dave18/SpecNext_MiSTER_Board/Source/rtl/zxnext.vhd

-- ZX Spectrum Next Implementation
-- Copyright 2020 Alvin Albrecht, Victor Trucco and Fabio Belavenuto
--
-- TBBlue - Victor Trucco & Fabio Belavenuto
-- ZXNext Refactor - Alvin Albrecht
--
-- This file is part of the ZX Spectrum Next Project
-- <https://gitlab.com/SpectrumNext/ZX_Spectrum_Next_FPGA/tree/master/cores>
--
-- The ZX Spectrum Next FPGA source code is free software: you can 
-- redistribute it and/or modify it under the terms of the GNU General 
-- Public License as published by the Free Software Foundation, either 
-- version 3 of the License, or (at your option) any later version.
--
-- The ZX Spectrum Next FPGA source code is distributed in the hope 
-- that it will be useful, but WITHOUT ANY WARRANTY; without even the 
-- implied warranty of MERCHANTABILITY or FITNESS FOR A PARTICULAR 
-- PURPOSE.  See the GNU General Public License for more details.
--
-- You should have received a copy of the GNU General Public License
-- along with the ZX Spectrum Next FPGA source code.  If not, see 
-- <https://www.gnu.org/licenses/>.

library ieee;
use ieee.std_logic_1164.all;
use IEEE.NUMERIC_STD.ALL;
use IEEE.std_logic_unsigned.ALL;
use work.Z80N_pack.all;

entity zxnext is
   generic
   (
      g_machine_id         : unsigned(7 downto 0);
      g_version            : unsigned(7 downto 0);
      g_sub_version        : unsigned(7 downto 0)
   );
   port (
      -- CLOCK
      
      i_CLK_28             : in std_logic;      -- 28MHz for machine logic
      i_CLK_28_n           : in std_logic;      -- 28MHz inverted
      i_CLK_14             : in std_logic;      -- 14MHz hi-res pixel clock
      i_CLK_7              : in std_logic;      -- 7MHz pixel clock
      i_CLK_CPU            : in std_logic;      -- CPU clock adjusted for speed and contention
      i_CLK_PSG_EN         : in std_logic;      -- 28MHz clock enable for PSG

      o_CPU_SPEED          : out std_logic_vector(1 downto 0);    -- cpu speed selection 00 = 3.5, 01 = 7, 10 = 14, 11 = 28
      o_CPU_CONTEND        : out std_logic;     -- indicates cpu is contended
      o_CPU_CLK_LSB        : out std_logic;     -- the contended cpu clock is derived from the pixel counter lsb
      
      -- RESET

      i_RESET_HARD         : in std_logic;      -- reboot in config mode, duration counted in top module
      i_RESET_SOFT         : in std_logic;      -- reset current system, duration counted in top module
      
      o_RESET_SOFT         : out std_logic;     -- asserted for one cycle at 28MHz
      o_RESET_HARD         : out std_logic;     -- asserted for one cycle at 28MHz
      o_RESET_PERIPHERAL   : out std_logic;     -- asserted under sw control for esp / exp bus reset
      
      -- FLASH BOOT
      
      o_FLASH_BOOT         : out std_logic;                       -- load new core
      o_CORE_ID            : out std_logic_vector(4 downto 0);    -- core id 0-31
      
      -- SPECIAL KEYS

      i_SPKEY_FUNCTION     : in std_logic_vector(10 downto 1);    -- F10 through F1
      i_SPKEY_BUTTONS      : in std_logic_vector(1 downto 0);     -- raw state of nmi buttons m1(0) & drive(1)
      
      -- MEMBRANE KEYBOARD
      
      o_KBD_CANCEL         : out std_logic;                       -- cancel entering extended keys into standard 8x5 matrix
      
      o_KBD_ROW            : out std_logic_vector(7 downto 0);    -- A15:A8 in keyboard read
      i_KBD_COL            : in std_logic_vector(4 downto 0);     -- D4:D0 in keyboard read (D6:D5 are the new keys)
      
      i_KBD_EXTENDED_KEYS  : in std_logic_vector(15 downto 0);    -- state of extended keys independent of matrix
      
      -- PS/2 KEYBOARD SETUP
      
      o_KEYMAP_ADDR        : out std_logic_vector(8 downto 0);    -- keymap address
      o_KEYMAP_DATA        : out std_logic_vector(7 downto 0);    -- keymap data
      o_KEYMAP_WE          : out std_logic;                       -- write signal
      
      -- JOYSTICK
      
      i_JOY_LEFT           : in std_logic_vector(10 downto 0);    -- active high  X Z Y START A C B U D L R
      i_JOY_RIGHT          : in std_logic_vector(10 downto 0);    -- active high  X Z Y START A C B U D L R
      
      o_JOY_IO_MODE_EN     : out std_logic;                       -- joystick io mode enabled
      o_JOY_IO_MODE_PIN_7  : out std_logic;                       -- state of pin 7 if in joystick io mode
		
		o_JOY_LEFT_TYPE      : out std_logic_vector(2 downto 0);        -- left joystick type --additional code 
		o_JOY_RIGHT_TYPE     : out std_logic_vector(2 downto 0);        -- right joystick type --additional code
      
      -- MOUSE
      
      i_MOUSE_X            : in std_logic_vector(7 downto 0);
      i_MOUSE_Y            : in std_logic_vector(7 downto 0);
      i_MOUSE_BUTTON       : in std_logic_vector(2 downto 0);     -- M, R, L
      i_MOUSE_WHEEL        : in std_logic_vector(3 downto 0);
      
      o_PS2_MODE           : out std_logic;
      o_MOUSE_CONTROL      : out std_logic_vector(2 downto 0);    -- Button reverse, DPI(1:0)
      
      -- I2C
      
      i_I2C_SCL_n          : in std_logic;
      i_I2C_SDA_n          : in std_logic;
      
      o_I2C_SCL_n          : out std_logic;     -- 0 = assert, 1 = tristate
      o_I2C_SDA_n          : out std_logic;     -- 0 = assert, 1 = tristate
      
      -- SPI

      o_SPI_SS_FLASH_n     : out std_logic;
      o_SPI_SS_SD1_n       : out std_logic;
      o_SPI_SS_SD0_n       : out std_logic;

      o_SPI_SCK            : out std_logic;
      o_SPI_MOSI           : out std_logic;
      
      i_SPI_SD_MISO        : in std_logic;
      i_SPI_FLASH_MISO     : in std_logic;
      
      -- UART
      
      i_UART0_RX           : in std_logic;
      o_UART0_TX           : out std_logic;
      
      -- VIDEO
      -- synchronized to i_CLK_14
      
      o_RGB                : out std_logic_vector(8 downto 0);    -- RGB333
      o_RGB_CS_n           : out std_logic;                       -- csync
      o_RGB_VS_n           : out std_logic;                       -- vsync
      o_RGB_HS_n           : out std_logic;                       -- hsync
      o_RGB_VB_n           : out std_logic;                       -- vblank
      o_RGB_HB_n           : out std_logic;                       -- hblank
      
      o_VIDEO_50_60        : out std_logic;                       -- 0 = 50Hz, 1 = 60Hz
      o_VIDEO_SCANLINES    : out std_logic_vector(1 downto 0);    -- 
      o_VIDEO_SCANDOUBLE   : out std_logic;                       -- 
      
      o_VIDEO_MODE         : out std_logic_vector(2 downto 0);    -- video mode: VGA 0-6, HDMI
      o_MACHINE_TIMING     : out std_logic_vector(2 downto 0);    -- machine timing: 00X = 48k, 010 = 128k, 011 = +3, 100 = pentagon
      
      o_HDMI_RESET         : out std_logic;
      
      -- AUDIO
      
      o_AUDIO_HDMI_AUDIO_EN : out std_logic;

      o_AUDIO_SPEAKER_EN   : out std_logic;     -- enable internal speaker
      o_AUDIO_SPEAKER_BEEP : out std_logic;     -- only beep to internal speaker
      
      i_AUDIO_EAR          : in std_logic;      -- tape in
      o_AUDIO_MIC          : out std_logic;     -- tape out
      
      o_AUDIO_SPEAKER_EAR  : out std_logic;
      o_AUDIO_SPEAKER_MIC  : out std_logic;

      o_AUDIO_L            : out std_logic_vector(12 downto 0);   -- pcm audio
      o_AUDIO_R            : out std_logic_vector(12 downto 0);   -- pcm audio

      -- EXTERNAL SRAM (synchronized to i_CLK_28)
      -- memory transactions complete after one cycle, data read is registered a cycle later but is available asap
      
      -- Port A is read/write and highest priority (CPU)
      
      o_RAM_A_ADDR         : out std_logic_vector(20 downto 0);   -- 2MB memory space
      o_RAM_A_REQ          : out std_logic;                       -- '1' indicates memory request on next rising edge
      o_RAM_A_RD           : out std_logic;                       -- '1' for read, '0' for write
      i_RAM_A_DI           : in std_logic_vector(7 downto 0);     -- data read from memory
      o_RAM_A_DO           : out std_logic_vector(7 downto 0);    -- data written to memory
		
		i_CPU_WAIT           : in std_logic := '0';
      
      -- Port B is read only (LAYER 2)
      
      o_RAM_B_ADDR         : out std_logic_vector(20 downto 0);   -- 2MB memory space
      o_RAM_B_REQ_T        : out std_logic;                       -- toggle indicates memory request
      i_RAM_B_DI           : in std_logic_vector(7 downto 0);     -- data read from memory
      
      -- EXPANSION BUS
      
      o_BUS_ADDR           : out std_logic_vector(15 downto 0);   -- unidirectional address bus = no external DMA for now
      i_BUS_DI             : in std_logic_vector(7 downto 0);     -- data bus in from external connector
      o_BUS_DO             : out std_logic_vector(7 downto 0);    -- data bus out to external connector
      o_BUS_MREQ_n         : out std_logic;
      o_BUS_IORQ_n         : out std_logic;
      o_BUS_RD_n           : out std_logic;
      o_BUS_WR_n           : out std_logic;
      o_BUS_M1_n           : out std_logic;
      i_BUS_WAIT_n         : in std_logic;
      i_BUS_NMI_n          : in std_logic;
      i_BUS_INT_n          : in std_logic;
      o_BUS_INT_n          : out std_logic;
      i_BUS_BUSREQ_n       : in std_logic;
      o_BUS_BUSAK_n        : out std_logic;
      o_BUS_HALT_n         : out std_logic;
      o_BUS_RFSH_n         : out std_logic;
--    o_BUS_IEO            : out std_logic;
      
      i_BUS_ROMCS_n        : in std_logic;                        -- 1 disables internal rom
--    i_BUS_RAMCS_n        : in std_logic;
      i_BUS_IORQULA_n      : in std_logic;                        -- 1 disables port fe
      
      o_BUS_EN             : out std_logic;                       -- enable the expansion bus, changes on rising edge of cpu clock
      o_BUS_CLKEN          : out std_logic;                       -- 1 to keep 3.5MHz clock on the expansion bus even when off
      
      o_BUS_NMI_DEBOUNCE_DISABLE  : out std_logic;
      
      -- ESP GPIO
      
      i_ESP_GPIO_20        : in std_logic_vector(2 downto 0);
      
      o_ESP_GPIO_0         : out std_logic;
      o_ESP_GPIO_0_EN      : out std_logic;                       -- 0 = high Z
      
      -- PI GPIO
      
      i_GPIO               : in std_logic_vector(27 downto 0);
      
      o_GPIO               : out std_logic_vector(27 downto 0);
      o_GPIO_EN            : out std_logic_vector(27 downto 0)    -- 0 = high Z
   );
end entity;

architecture rtl of zxnext is

   -- RESET
   
   signal reset                  : std_logic;
   signal reset_soft             : std_logic;
   signal reset_hard             : std_logic;
   
   -- Z80 & DMA
   
   signal z80_wait_n             : std_logic;
   signal z80_int_n              : std_logic;
   signal z80_nmi_n              : std_logic;
   signal z80_busrq_n            : std_logic;
   signal z80_m1_n               : std_logic;
   signal z80_mreq_n             : std_logic;
   signal z80_iorq_n             : std_logic;
   signal z80_rd_n               : std_logic;
   signal z80_wr_n               : std_logic;
   signal z80_rfsh_n             : std_logic;
   signal z80_halt_n             : std_logic;
   signal z80_busak_n            : std_logic;
   signal z80_a                  : std_logic_vector(15 downto 0);
   signal z80_do                 : std_logic_vector(7 downto 0);
   signal Z80N_dout_s            : std_logic;
   signal Z80N_data_s            : std_logic_vector(15 downto 0);
   signal Z80N_command_s         : Z80N_seq;

   signal dma_wait_n             : std_logic;
   signal dma_busrq_n            : std_logic;
   signal dma_a                  : std_logic_vector(15 downto 0);
   signal dma_do                 : std_logic_vector(7 downto 0);
   signal dma_rd_n               : std_logic;
   signal dma_wr_n               : std_logic;
   signal dma_mreq_n             : std_logic;
   signal dma_iorq_n             : std_logic;
   
   signal port_dma_dat_0         : std_logic_vector(7 downto 0);
   signal port_dma_dat           : std_logic_vector(7 downto 0);
   signal dma_mode               : std_logic := '0';
   
   signal dma_holds_bus          : std_logic;
   signal cpu_m1_n               : std_logic;
   signal cpu_mreq_n             : std_logic;
   signal cpu_iorq_n             : std_logic;
   signal cpu_rd_n               : std_logic;
   signal cpu_wr_n               : std_logic;
   signal cpu_rfsh_n             : std_logic;
   signal cpu_halt_n             : std_logic;
   signal cpu_a                  : std_logic_vector(15 downto 0);
   signal cpu_di                 : std_logic_vector(7 downto 0);
   signal cpu_do                 : std_logic_vector(7 downto 0);
   
   signal im2_ieo                : std_logic;
   signal im2_reti_decode        : std_logic;
   signal z80_reti_seen_t3       : std_logic;
   signal z80_retn_seen_t3       : std_logic;
   signal z80_retn_seen_28       : std_logic;
   signal z80_retn_seen_28_d     : std_logic;
   signal dma_delay              : std_logic;
   signal im2_dma_delay          : std_logic;
   
   signal im2_int_req            : std_logic_vector(13 downto 0);
   signal im2_int_en             : std_logic_vector(13 downto 0);
   signal im2_status_clear       : std_logic_vector(13 downto 0);
   signal im2_dma_int_en         : std_logic_vector(13 downto 0);
   signal im2_int_status         : std_logic_vector(13 downto 0);
   signal im2_int_n              : std_logic;
   signal pulse_int_en           : std_logic;
   signal im2_dma_int            : std_logic;
   signal im2_vec                : std_logic_vector(3 downto 0);
   signal im2_vector             : std_logic_vector(7 downto 0);
   signal im2_vector_en          : std_logic;
   
   signal z80_stackless_nmi      : std_logic;
   signal z80_retn_address       : std_logic_vector(7 downto 0);
   
   signal nmi_activated          : std_logic;
   signal nmi_expbus_en          : std_logic;
   signal nmi_assert_expbus      : std_logic;
   signal nmi_mf                 : std_logic := '0';
   signal nmi_divmmc             : std_logic := '0';
   signal nmi_expbus             : std_logic := '0';
   signal nmi_hold               : std_logic;
   
   type   nmi_state_t            is (S_NMI_IDLE, S_NMI_ASSERT, S_NMI_OPUS, S_NMI_HOLD, S_NMI_END);
   signal nmi_state              : nmi_state_t := S_NMI_IDLE;
   signal nmi_state_next         : nmi_state_t;
   signal nmi_holding            : std_logic;
   signal nmi_opus               : std_logic;
   signal nmi_generate_n         : std_logic;
   signal nmi_mf_button          : std_logic;
   signal nmi_divmmc_button      : std_logic;
   
   -- EXPANSION BUS
   
   signal nr_80_expbus           : std_logic_vector(7 downto 0) := X"00";

   signal expbus_en              : std_logic;
   signal expbus_romcs_replace   : std_logic;
   signal expbus_disable_io      : std_logic;
   signal expbus_disable_mem     : std_logic;
   signal expbus_clken           : std_logic;
   signal expbus_speed           : std_logic_vector(1 downto 0);
   
   signal expbus_eff_en          : std_logic := '0';
   signal expbus_eff_disable_io  : std_logic := '0';
   signal expbus_eff_disable_mem : std_logic := '0';
   signal expbus_eff_clken       : std_logic := '0';
   
   signal port_propagate_fe      : std_logic;
   signal port_propagate_7ffd    : std_logic;
   signal port_propagate_dffd    : std_logic;
   signal port_propagate_1ffd    : std_logic;
   signal port_propagate_ff      : std_logic;
   signal port_propagate_eff7    : std_logic;
   
   signal port_propagate         : std_logic;
   signal bus_iorq_n             : std_logic;
   signal bus_mreq_n             : std_logic;
   
   -- ALTERNATIVE ROM
   
   signal nr_8c_altrom           : std_logic_vector(7 downto 0) := X"00";
   
   signal nr_8c_altrom_en        : std_logic;
   signal nr_8c_altrom_rw        : std_logic;
   signal nr_8c_altrom_lock_rom1 : std_logic;
   signal nr_8c_altrom_lock_rom0 : std_logic;

   -- PI GPIO
   
   signal pi_gpio_en             : std_logic_vector(27 downto 0);
   signal pi_gpio_o              : std_logic_vector(27 downto 0);
   
   signal pi_uart_rxtx           : std_logic;
   signal pi_uart_en             : std_logic;
   signal pi_i2c1_en             : std_logic;
   signal pi_spi0_en             : std_logic;
   
   signal pi_i2s_en              : std_logic;
   signal pi_i2s_enL             : std_logic;
   signal pi_i2s_enR             : std_logic;
   signal pi_i2s_inout           : std_logic;
   signal pi_i2s_muteL           : std_logic;
   signal pi_i2s_muteR           : std_logic;
-- signal pi_i2s_slave           : std_logic;
   signal pi_i2s_ear             : std_logic;
   
   signal gpio_07_en             : std_logic;
   signal gpio_07                : std_logic;
   signal gpio_08_en             : std_logic;
   signal gpio_08                : std_logic;
   signal gpio_09_en             : std_logic;
   signal pi_spi0_miso           : std_logic;
   signal gpio_10_en             : std_logic;
   signal gpio_10                : std_logic;
   signal gpio_11_en             : std_logic;
   signal gpio_11                : std_logic;
   
   signal gpio_02_en             : std_logic;
   signal gpio_02                : std_logic;
   signal gpio_03_en             : std_logic;
   signal gpio_03                : std_logic;
   signal pi_i2c1_sda            : std_logic;
   signal pi_i2c1_scl            : std_logic;
   
   signal gpio_14_en             : std_logic;
   signal gpio_14                : std_logic;
   signal gpio_15_en             : std_logic;
   signal gpio_15                : std_logic;
   signal gpio_16_en             : std_logic;
   signal gpio_16                : std_logic;
   signal gpio_17_en             : std_logic;
   signal gpio_17                : std_logic;
   signal pi_uart_rx             : std_logic;
   signal pi_uart_cts_n          : std_logic;
   
   signal gpio_18_en             : std_logic;
   signal gpio_18                : std_logic;
   signal gpio_19_en             : std_logic;
   signal gpio_19                : std_logic;
   signal gpio_20_en             : std_logic;
   signal gpio_20                : std_logic;
   signal gpio_21_en             : std_logic;
   signal gpio_21                : std_logic;
   
   signal pi_audio_L             : std_logic_vector(9 downto 0);
   signal pi_audio_R             : std_logic_vector(9 downto 0);
   signal pi_fe_threshold        : std_logic_vector(1 downto 0);
   signal pi_fe_ear              : std_logic;
   
   -- PORT DECODING
   
   signal internal_port_enable   : std_logic_vector(27 downto 0);
   
   signal port_ff_io_en          : std_logic;
   signal port_7ffd_io_en        : std_logic;
   signal port_dffd_io_en        : std_logic;
   signal port_1ffd_io_en        : std_logic;
   signal port_p3_floating_bus_io_en         : std_logic;
   signal port_dma_6b_io_en      : std_logic;
   signal port_1f_io_en          : std_logic;
   signal port_37_io_en          : std_logic;
   signal port_divmmc_io_en      : std_logic;
   signal port_divmmc_io_en_diff             : std_logic;
   signal port_multiface_io_en   : std_logic;
   signal port_multiface_io_en_diff          : std_logic;
   signal port_i2c_io_en         : std_logic;
   signal port_spi_io_en         : std_logic;
   signal port_uart_io_en        : std_logic;
   signal port_mouse_io_en       : std_logic;
   signal port_sprite_io_en      : std_logic;
   signal port_layer2_io_en      : std_logic;
   signal port_ay_io_en          : std_logic;
   signal port_dac_sd1_ABCD_1f0f4f5f_io_en   : std_logic;
   signal port_dac_sd2_ABCD_f1f3f9fb_io_en   : std_logic;
   signal port_dac_stereo_AD_3f5f_io_en      : std_logic;
   signal port_dac_stereo_BC_0f4f_io_en      : std_logic;
   signal port_dac_mono_AD_fb_io_en          : std_logic;
   signal port_dac_mono_BC_b3_io_en          : std_logic;
   signal port_dac_mono_AD_df_io_en          : std_logic;
   signal port_ulap_io_en        : std_logic;
   signal port_dma_0b_io_en      : std_logic;
   signal port_eff7_io_en        : std_logic;
   signal port_ctc_io_en         : std_logic;
   
   signal port_1f_hw_en          : std_logic;
   signal port_37_hw_en          : std_logic;
   signal p3_timing_hw_en        : std_logic;
   signal s128_timing_hw_en      : std_logic;
   signal dac_hw_en              : std_logic;
   
   signal bus_iorq_ula           : std_logic := '0';

   signal port_00xx_msb          : std_logic;
   signal port_04xx_msb          : std_logic;
   signal port_05xx_msb          : std_logic;
   signal port_10xx_msb          : std_logic;
   signal port_11xx_msb          : std_logic;
   signal port_12xx_msb          : std_logic;
   signal port_1fxx_msb          : std_logic;
   signal port_24xx_msb          : std_logic;
   signal port_25xx_msb          : std_logic;
   signal port_30xx_msb          : std_logic;
   signal port_3dxx_msb          : std_logic;
   signal port_7fxx_msb          : std_logic;
   signal port_bfxx_msb          : std_logic;
   signal port_fexx_msb          : std_logic;
   signal port_ffxx_msb          : std_logic;

   signal port_00_lsb            : std_logic;
   signal port_08_lsb            : std_logic;
   signal port_0b_lsb            : std_logic;
   signal port_0f_lsb            : std_logic;
   signal port_1f_lsb            : std_logic;
   signal port_37_lsb            : std_logic;
   signal port_38_lsb            : std_logic;
   signal port_3f_lsb            : std_logic;
   signal port_3b_lsb            : std_logic;
   signal port_4f_lsb            : std_logic;
   signal port_57_lsb            : std_logic;
   signal port_5b_lsb            : std_logic;
   signal port_5f_lsb            : std_logic;
   signal port_62_lsb            : std_logic;
   signal port_66_lsb            : std_logic;
   signal port_6b_lsb            : std_logic;
   signal port_b3_lsb            : std_logic;
   signal port_c6_lsb            : std_logic;
   signal port_df_lsb            : std_logic;
   signal port_e3_lsb            : std_logic;
   signal port_e7_lsb            : std_logic;
   signal port_eb_lsb            : std_logic;
   signal port_f1_lsb            : std_logic;
   signal port_f3_lsb            : std_logic;
   signal port_f7_lsb            : std_logic;
   signal port_f9_lsb            : std_logic;
   signal port_fb_lsb            : std_logic;
   signal port_ff_lsb            : std_logic;
   
   signal port_fe                : std_logic;
   signal port_ff                : std_logic;
   signal port_fe_override       : std_logic;
   signal port_fd                : std_logic;
   signal port_p3_float          : std_logic;
-- signal port_p3_float_active   : std_logic;
   signal port_7ffd              : std_logic;
   signal port_7ffd_active       : std_logic;
   signal port_7ffd_assert       : std_logic;
   signal port_dffd              : std_logic;
   signal port_1ffd              : std_logic;
-- signal port_1ffd_active       : std_logic;
   signal port_1ffd_assert       : std_logic;
   signal port_eff7              : std_logic;
   signal port_e3                : std_logic;
   signal port_mf_enable_io_a    : std_logic_vector(7 downto 0);
   signal port_mf_disable_io_a   : std_logic_vector(7 downto 0);
   signal port_mf_enable         : std_logic;
   signal port_mf_disable        : std_logic;
   signal port_e7                : std_logic;
   signal port_eb                : std_logic;
   signal port_243b              : std_logic;
   signal port_253b              : std_logic;
   signal port_103b              : std_logic;
   signal port_113b              : std_logic;
   signal port_123b              : std_logic;
   signal port_uart              : std_logic;
   signal port_dma               : std_logic;
   signal port_fffd              : std_logic;
   signal port_bffd              : std_logic;
   signal port_bff5              : std_logic;
   signal port_dac_mono_AD       : std_logic;
   signal port_dac_mono_BC       : std_logic;
   signal port_dac_A             : std_logic;
   signal port_dac_B             : std_logic;
   signal port_dac_C             : std_logic;
   signal port_dac_D             : std_logic;
   signal port_fadf              : std_logic;
   signal port_fbdf              : std_logic;
   signal port_ffdf              : std_logic;
   signal port_1f                : std_logic;
   signal port_37                : std_logic;
   signal port_57                : std_logic;
   signal port_5b                : std_logic;
   signal port_303b              : std_logic;
   signal port_bf3b              : std_logic;
   signal port_ff3b              : std_logic;
   signal port_ctc               : std_logic;
   signal port_internal_response : std_logic;
   
   signal iord                   : std_logic;
   signal iowr                   : std_logic;
   
   signal port_fd_conflict_wr    : std_logic;
   
   signal port_fe_rd             : std_logic;
   signal port_fe_wr             : std_logic;
   signal port_ff_rd             : std_logic;
   signal port_ff_wr             : std_logic;
   signal port_p3_float_rd       : std_logic;
   signal port_7ffd_wr           : std_logic;
   signal port_dffd_wr           : std_logic;
   signal port_1ffd_wr           : std_logic;
   signal port_eff7_wr           : std_logic;
   signal port_e3_rd             : std_logic;
   signal port_e3_wr             : std_logic;
   signal port_mf_enable_rd      : std_logic;
   signal port_mf_enable_wr      : std_logic;
   signal port_mf_disable_rd     : std_logic;
   signal port_mf_disable_wr     : std_logic;
   signal port_e7_wr             : std_logic;
   signal port_eb_rd             : std_logic;
   signal port_eb_wr             : std_logic;
   signal port_243b_rd           : std_logic;
   signal port_243b_wr           : std_logic;
   signal port_253b_rd           : std_logic;
   signal port_253b_wr           : std_logic;
   signal port_103b_rd           : std_logic;
   signal port_103b_wr           : std_logic;
   signal port_113b_rd           : std_logic;
   signal port_113b_wr           : std_logic;
   signal port_123b_rd           : std_logic;
   signal port_123b_wr           : std_logic;
   signal port_uart_rd           : std_logic;
   signal port_uart_wr           : std_logic;
   signal port_dma_rd            : std_logic;
   signal port_dma_wr            : std_logic;
   signal port_fffd_rd           : std_logic;
   signal port_fffd_wr           : std_logic;
   signal port_bffd_wr           : std_logic;
   signal port_dac_A_wr          : std_logic;
   signal port_dac_B_wr          : std_logic;
   signal port_dac_C_wr          : std_logic;
   signal port_dac_D_wr          : std_logic;
   signal port_fadf_rd           : std_logic;
   signal port_fbdf_rd           : std_logic;
   signal port_ffdf_rd           : std_logic;
   signal port_1f_rd             : std_logic;
   signal port_37_rd             : std_logic;
   signal port_37_wr             : std_logic;
   signal port_57_wr             : std_logic;
   signal port_5b_wr             : std_logic;
   signal port_303b_rd           : std_logic;
   signal port_303b_wr           : std_logic;
   signal port_bf3b_wr           : std_logic;
   signal port_ff3b_rd           : std_logic;
   signal port_ff3b_wr           : std_logic;
   signal port_ctc_wr            : std_logic;
   signal port_ctc_rd            : std_logic;

   signal port_internal_rd_response          : std_logic;
   
   signal port_fe_rd_dat         : std_logic_vector(7 downto 0);
   signal port_ff_rd_dat         : std_logic_vector(7 downto 0);
   signal port_p3_float_rd_dat   : std_logic_vector(7 downto 0);
   signal port_e3_rd_dat         : std_logic_vector(7 downto 0);
   signal port_mf_rd_dat         : std_logic_vector(7 downto 0);
   signal port_eb_rd_dat         : std_logic_vector(7 downto 0);
   signal port_243b_rd_dat       : std_logic_vector(7 downto 0);
   signal port_253b_rd_dat       : std_logic_vector(7 downto 0);
   signal port_103b_rd_dat       : std_logic_vector(7 downto 0);
   signal port_113b_rd_dat       : std_logic_vector(7 downto 0);
   signal port_123b_rd_dat       : std_logic_vector(7 downto 0);
   signal port_uart_rd_dat       : std_logic_vector(7 downto 0);
   signal port_dma_rd_dat        : std_logic_vector(7 downto 0);
   signal port_fffd_rd_dat       : std_logic_vector(7 downto 0);
   signal port_fadf_rd_dat       : std_logic_vector(7 downto 0);
   signal port_fbdf_rd_dat       : std_logic_vector(7 downto 0);
   signal port_ffdf_rd_dat       : std_logic_vector(7 downto 0);
   signal port_1f_rd_dat         : std_logic_vector(7 downto 0);
   signal port_37_rd_dat         : std_logic_vector(7 downto 0);
   signal port_303b_rd_dat       : std_logic_vector(7 downto 0);
   signal port_ff3b_rd_dat       : std_logic_vector(7 downto 0);
   signal port_ctc_rd_dat        : std_logic_vector(7 downto 0);
   
   signal port_rd_dat            : std_logic_vector(7 downto 0);

   -- MEMORY ADDRESSES

   signal divmmc_automap_en_instant             : std_logic;
   signal divmmc_automap_en_delayed             : std_logic;
   signal divmmc_automap_en_delayed_nohide      : std_logic;
   signal divmmc_automap_en_delayed_nohide_nmi  : std_logic;
   signal divmmc_automap_dis_delayed            : std_logic;

   signal mf_a_0066              : std_logic;
   signal mf_a_1fxx              : std_logic;
   signal mf_a_7fxx              : std_logic;
   signal mf_a_fexx              : std_logic;

   -- MEMORY DECODING
   
   signal mem_active_page        : std_logic_vector(7 downto 0);
   
   signal layer2_active_bank_offset_pre      : std_logic_vector(1 downto 0);
   signal layer2_active_bank_offset          : std_logic_vector(3 downto 0);
   signal layer2_active_bank     : std_logic_vector(6 downto 0);
   signal layer2_active_page     : std_logic_vector(8 downto 0);
   
   signal sram_config_active     : std_logic;
   
   signal mmu_A21_A13            : std_logic_vector(8 downto 0);
   signal layer2_A21_A13         : std_logic_vector(8 downto 0);
   
   signal mem_active_bank5       : std_logic;
   signal mem_active_bank7       : std_logic;
   signal sram_active_rom        : std_logic_vector(1 downto 0);
   signal sram_rom3              : std_logic;
   signal sram_alt_128           : std_logic;
   signal eff_expbus_romcs_replace           : std_logic;
   
   signal layer2_pre_A21_A13     : std_logic_vector(8 downto 0);
   signal sram_pre_active        : std_logic;
   signal sram_pre_rom3          : std_logic;
   signal sram_pre_bank5         : std_logic;
   signal sram_pre_bank7         : std_logic;
   signal sram_pre_rdonly        : std_logic;
   signal sram_pre_romcs         : std_logic;
   signal sram_pre_alt_en        : std_logic;
   signal sram_pre_alt_128       : std_logic;
   signal port_123b_layer2_map_rd_pre        : std_logic;
   signal port_123b_layer2_map_wr_pre        : std_logic;
   signal port_123b_layer2_map_segment_pre   : std_logic_vector(1 downto 0);
   signal sram_pre_A20_A13       : std_logic_vector(7 downto 0);
   
   signal layer2_map_en          : std_logic;
   signal altrom_en              : std_logic;
   signal sram_A20_A13           : std_logic_vector(7 downto 0);
   signal sram_active            : std_logic;
   signal sram_bank5             : std_logic;
   signal sram_bank7             : std_logic;
   signal sram_rdonly            : std_logic;
   signal sram_romcs_en          : std_logic;
   signal sram_obscure_divmmc_automap        : std_logic;
   signal sram_disable_divmmc_automap        : std_logic;
   
   signal memcycle               : std_logic;
   signal memcycle_delay         : std_logic_vector(3 downto 0);
   signal memcycle_delay_end     : std_logic_vector(3 downto 0);
   signal memcycle_delay_complete            : std_logic;
   signal sram_romcs             : std_logic;
   signal cpu_bank5_rd           : std_logic;
   signal cpu_bank5_we           : std_logic;
   signal cpu_bank7_we           : std_logic;
   signal sram_addr              : std_logic_vector(20 downto 0);
   signal sram_rd                : std_logic;
   signal sram_req               : std_logic;
   signal sram_req_dly           : std_logic;
   signal sram_req_t             : std_logic;
   signal sram_wait_n            : std_logic := '1';
   
   signal bootrom_do             : std_logic_vector(7 downto 0);
   
   -- SERIAL COMMS
   
   signal i2c_scl_o              : std_logic;
   signal i2c_sda_o              : std_logic;
   signal port_103b_dat          : std_logic_vector(7 downto 0) := X"FF";
   signal port_113b_dat          : std_logic_vector(7 downto 0) := X"FF";

   signal spi_ss_flash_n         : std_logic;
   signal spi_ss_rpi1_n          : std_logic;
   signal spi_ss_rpi0_n          : std_logic;
   signal spi_ss_sd1_n           : std_logic;
   signal spi_ss_sd0_n           : std_logic;
   signal spi_sck                : std_logic;
   signal spi_mosi               : std_logic;
   signal spi_miso               : std_logic;
   signal spi_wait_n             : std_logic;
   signal port_eb_dat            : std_logic_vector(7 downto 0);
   signal port_e7_reg            : std_logic_vector(7 downto 0) := X"FF";
   
   signal uart0_tx_esp           : std_logic;
   signal uart1_tx_pi            : std_logic;
   signal pi_uart_rtr_n          : std_logic;
   
   signal uart_do                : std_logic_vector(7 downto 0);
   
   signal uart0_hwflow_en        : std_logic;
   signal uart0_rx               : std_logic;
   signal uart0_rx_rtr_n           : std_logic;
   signal uart0_rx_avail         : std_logic;
   signal uart0_rx_near_full     : std_logic;
   signal uart0_tx               : std_logic;
   signal uart0_tx_cts_n           : std_logic;
   signal uart0_tx_empty         : std_logic;
   
   signal uart1_hwflow_en        : std_logic;
   signal uart1_rx               : std_logic;
   signal uart1_rx_rtr_n         : std_logic;
   signal uart1_rx_avail         : std_logic;
   signal uart1_rx_near_full     : std_logic;
   signal uart1_tx               : std_logic;
   signal uart1_tx_cts_n         : std_logic;
   signal uart1_tx_empty         : std_logic;
   
   signal joy_iomode_hwflen      : std_logic;

   signal port_uart_dat          : std_logic_vector(7 downto 0);
   
   -- KEYBOARD, JOYSTICKS & MOUSE
   
   signal keyrow                 : std_logic_vector(7 downto 0);
   
   signal in_joy_left            : std_logic_vector(10 downto 0);
   signal in_joy_right           : std_logic_vector(10 downto 0);
   
   signal joyL_up                : std_logic;
   signal joyR_up                : std_logic;
   
   signal joyL_sinc1             : std_logic_vector(4 downto 0);
   signal joyL_sinc2             : std_logic_vector(4 downto 0);
   signal joyL_cursA             : std_logic_vector(4 downto 0);
   signal joyL_cursB             : std_logic_vector(4 downto 0);
   
   signal joyR_sinc1             : std_logic_vector(4 downto 0);
   signal joyR_sinc2             : std_logic_vector(4 downto 0);
   signal joyR_cursA             : std_logic_vector(4 downto 0);
   signal joyR_cursB             : std_logic_vector(4 downto 0);
   
   signal joy_key                : std_logic_vector(4 downto 0);
   
   signal port_fe_bus            : std_logic_vector(7 downto 0);
   signal port_fe_dat_0          : std_logic_vector(7 downto 0);
   signal port_fe_dat            : std_logic_vector(7 downto 0);
   
   signal mdL_1f_en              : std_logic;
   signal mdL_37_en              : std_logic;
   signal joyL_1f_en             : std_logic;
   signal joyL_37_en             : std_logic;
   signal joyL_1f                : std_logic_vector(7 downto 0);
   signal joyL_37                : std_logic_vector(7 downto 0);
   
   signal mdR_1f_en              : std_logic;
   signal mdR_37_en              : std_logic;
   signal joyR_1f_en             : std_logic;
   signal joyR_37_en             : std_logic;
   signal joyR_1f                : std_logic_vector(7 downto 0);
   signal joyR_37                : std_logic_vector(7 downto 0);
   
   signal joy_iomode             : std_logic_vector(1 downto 0) := "00";
   signal joy_iomode_0           : std_logic := '0';
   signal nr_05_joy_iomode_en    : std_logic := '0';
   signal joy_iomode_pin7        : std_logic := '1';
   signal joy_iomode_uart_en     : std_logic;
   signal joy_uart_rx            : std_logic;
   signal joy_uart_cts_n         : std_logic;
   
   signal port_1f_dat            : std_logic_vector(7 downto 0);
   signal port_37_dat            : std_logic_vector(7 downto 0);
   signal port_fbdf_dat          : std_logic_vector(7 downto 0);
   signal port_ffdf_dat          : std_logic_vector(7 downto 0);
   signal port_fadf_dat          : std_logic_vector(7 downto 0);
   
   -- DEVICES
   
   signal port_fe_reg            : std_logic_vector(4 downto 0);
   signal port_fe_ear            : std_logic;
   signal port_fe_mic            : std_logic;
   signal port_fe_border         : std_logic_vector(2 downto 0) := "000";
   
   signal port_ff_reg            : std_logic_vector(7 downto 0);
   signal port_ff_screen_mode    : std_logic_vector(5 downto 0);
   signal port_ff_interrupt_disable          : std_logic;
   
   signal port_7ffd_reg          : std_logic_vector(7 downto 0);
   signal port_7ffd_dat          : std_logic_vector(7 downto 0);
   signal port_7ffd_bank         : std_logic_vector(6 downto 0);
   signal port_7ffd_shadow       : std_logic;
   signal port_7ffd_locked       : std_logic;
   
   signal port_dffd_reg          : std_logic_vector(4 downto 0);
   signal port_dffd_reg_6        : std_logic;
   
   signal port_1ffd_reg          : std_logic_vector(7 downto 0);
   signal port_1ffd_dat          : std_logic_vector(7 downto 0);
   signal port_1ffd_special      : std_logic;
   signal port_1ffd_special_old  : std_logic;
   signal port_1ffd_rom          : std_logic_vector(1 downto 0);
   
   signal port_eff7_reg_2        : std_logic;
   signal port_eff7_reg_3        : std_logic;

   signal nr_8f_mapping_mode     : std_logic_vector(1 downto 0) := (others => '0');
   signal nr_8f_mapping_mode_profi           : std_logic;
   signal nr_8f_mapping_mode_pentagon        : std_logic;
   signal nr_8f_mapping_mode_pentagon_1024   : std_logic;
   signal nr_8f_mapping_mode_pentagon_1024_en: std_logic;

   signal port_memory_change_dly : std_logic := '0';
   signal port_memory_ram_change_dly         : std_logic := '0';
   signal nr_8f_we_dly           : std_logic := '0';
   
   signal port_123b_dat          : std_logic_vector(7 downto 0) := (others => '0');
   signal port_123b_layer2_en    : std_logic;
   signal port_123b_layer2_map_wr_en         : std_logic;
   signal port_123b_layer2_map_rd_en         : std_logic;
   signal port_123b_layer2_map_shadow        : std_logic;
   signal port_123b_layer2_map_segment       : std_logic_vector(1 downto 0);
   signal port_123b_layer2_offset            : std_logic_vector(2 downto 0);
   
   signal copper_instr_addr      : std_logic_vector(9 downto 0);
   signal copper_dout_en         : std_logic;
   signal copper_dout            : std_logic_vector(14 downto 0);
   signal copper_instr_data      : std_logic_vector(15 downto 0);
   signal copper_msb_we          : std_logic;
   signal copper_msb_dat         : std_logic_vector(7 downto 0);
   signal copper_lsb_we          : std_logic;
   signal copper_lsb_dat         : std_logic_vector(7 downto 0);
   
   signal ctc_do                 : std_logic_vector(7 downto 0);
   signal port_ctc_dat           : std_logic_vector(7 downto 0);
   signal ctc_zc_to              : std_logic_vector(7 downto 0);
   signal ctc_int_en             : std_logic_vector(7 downto 0);
   
   signal divmmc_rom_en          : std_logic;
   signal divmmc_ram_en          : std_logic;
   signal divmmc_rdonly          : std_logic;
   signal divmmc_bank            : std_logic_vector(3 downto 0);
   signal port_e3_reg            : std_logic_vector(7 downto 0);
   signal port_e3_dat            : std_logic_vector(7 downto 0);
   signal divmmc_nmi_hold        : std_logic;
   signal divmmc_automap_held    : std_logic;
   signal divmmc_retn_seen       : std_logic;
   
   signal layer2_addr            : std_logic_vector(16 downto 0);
   signal layer2_pixel_en        : std_logic;
   signal layer2_addr_eff        : std_logic_vector(20 downto 0);
   signal layer2_req_t           : std_logic;
   signal layer2_pixel           : std_logic_vector(7 downto 0);
   
   signal lores_mode_0           : std_logic;
   signal lores_dfile_0          : std_logic;
   signal lores_palette_offset_0 : std_logic_vector(3 downto 0);
   signal lores_addr             : std_logic_vector(13 downto 0);
   signal lores_vram_di          : std_logic_vector(7 downto 0);
   signal lores_pixel            : std_logic_vector(7 downto 0);
   signal lores_pixel_en         : std_logic;
   signal lores_scroll_x_0       : std_logic_vector(7 downto 0);
   signal lores_scroll_y_0       : std_logic_vector(7 downto 0);
-- signal lores_clip_x1_0        : std_logic_vector(7 downto 0);
-- signal lores_clip_x2_0        : std_logic_vector(7 downto 0);
-- signal lores_clip_y1_0        : std_logic_vector(7 downto 0);
-- signal lores_clip_y2_0        : std_logic_vector(7 downto 0);
   
   signal mf_mem_en              : std_logic;
   signal mf_nmi_hold            : std_logic;
   signal mf_port_en             : std_logic;
   signal mf_port_dat            : std_logic_vector(7 downto 0);
   signal mf_is_active           : std_logic;
   
   signal port_303b_dat          : std_logic_vector(7 downto 0);
   signal sprite_mirror_id       : std_logic_vector(6 downto 0);
   signal sprite_pixel           : std_logic_vector(7 downto 0);
   signal sprite_pixel_en        : std_logic;
   
   signal sc                     : std_logic_vector(1 downto 0);
   signal tm_mem_bank7           : std_logic;
   signal tm_vram_a              : std_logic_vector(13 downto 0);
   signal tm_vram_rd             : std_logic;
   signal tm_vram_ack            : std_logic;
   signal tm_vram_di             : std_logic_vector(7 downto 0);
   signal tm_pixel               : std_logic_vector(7 downto 0);
   signal tm_pixel_en            : std_logic;
   signal tm_pixel_below         : std_logic;
   signal tm_pixel_textmode      : std_logic;
   
   signal ula_wait_n             : std_logic;
   signal ula_cpu_contend        : std_logic;
   signal ula_floating_bus       : std_logic_vector(7 downto 0);
   signal ula_vram_shadow        : std_logic;
   signal ula_vram_rd            : std_logic;
   signal ula_vram_a             : std_logic_vector(13 downto 0);
   signal ula_vram_di            : std_logic_vector(7 downto 0);
   signal ula_clip_x1_0          : std_logic_vector(7 downto 0);
   signal ula_clip_x2_0          : std_logic_vector(7 downto 0);
   signal ula_clip_y1_0          : std_logic_vector(7 downto 0);
   signal ula_clip_y2_0          : std_logic_vector(7 downto 0);
   signal ula_border             : std_logic;
   signal ula_pixel              : std_logic_vector(7 downto 0);
   signal ula_select_bgnd        : std_logic;
   signal ula_clipped            : std_logic;
   
   signal mem_contend            : std_logic;
   signal port_contend           : std_logic;
   signal p3_floating_bus_dat    : std_logic_vector(7 downto 0);
   signal port_ff_dat_ula        : std_logic_vector(7 downto 0);
   signal port_ff_dat_tmx        : std_logic_vector(7 downto 0);
   signal port_p3_floating_bus_dat           : std_logic_vector(7 downto 0);
   
   signal port_bf3b_ulap_mode    : std_logic_vector(1 downto 0);
   signal port_bf3b_ulap_index   : std_logic_vector(5 downto 0);
   signal port_ff3b_ulap_en      : std_logic;
   signal ulap_palette_rd        : std_logic;
   signal ulap_palette_rd_dly    : std_logic;
   signal ulap_palette_rd_done   : std_logic;
   signal ulap_wait_n            : std_logic;
   signal port_ff3b_dat          : std_logic_vector(7 downto 0);
   
   -- TBBLUE REGISTRY
   
   signal nr_register            : std_logic_vector(7 downto 0);
   signal port_243b_dat          : std_logic_vector(7 downto 0);
   
   signal MMU0                   : std_logic_vector(7 downto 0);
   signal MMU1                   : std_logic_vector(7 downto 0);
   signal MMU2                   : std_logic_vector(7 downto 0);
   signal MMU3                   : std_logic_vector(7 downto 0);
   signal MMU4                   : std_logic_vector(7 downto 0);
   signal MMU5                   : std_logic_vector(7 downto 0);
   signal MMU6                   : std_logic_vector(7 downto 0);
   signal MMU7                   : std_logic_vector(7 downto 0);
   
   signal copper_requester       : std_logic;
   signal copper_req_dly         : std_logic;
   signal copper_req             : std_logic;
   signal copper_nr_reg          : std_logic_vector(7 downto 0);
   signal copper_nr_dat          : std_logic_vector(7 downto 0);
   signal cpu_requester_0        : std_logic;
   signal cpu_requester_1        : std_logic;
   signal cpu_requester_2        : std_logic;
   signal cpu_req_dly            : std_logic;
   signal cpu_req                : std_logic;
   signal cpu_nr_reg             : std_logic_vector(7 downto 0);
   signal cpu_nr_dat             : std_logic_vector(7 downto 0);
   signal nr_wr_en               : std_logic;
   signal nr_wr_reg              : std_logic_vector(7 downto 0);
   signal nr_wr_dat              : std_logic_vector(7 downto 0);
   signal cpu_served             : std_logic;
   
   signal nr_02_we               : std_logic;
   signal nr_05_we               : std_logic;
   signal nr_07_we               : std_logic;
   signal nr_08_we               : std_logic;
   signal nr_09_we               : std_logic;
   signal nr_28_we               : std_logic;
   signal nr_29_we               : std_logic;
   signal nr_2a_we               : std_logic;
   signal nr_2b_we               : std_logic;
   signal nr_2c_we               : std_logic;
   signal nr_2d_we               : std_logic;
   signal nr_2e_we               : std_logic;
   signal nr_22_we               : std_logic;
   signal nr_41_we               : std_logic;
   signal nr_44_we               : std_logic;
   signal nr_sprite_mirror_we    : std_logic;
   signal nr_sprite_mirror_index : std_logic_vector(2 downto 0);
   signal nr_sprite_mirror_inc   : std_logic;
   signal nr_palette_we          : std_logic;
   signal nr_palette_value       : std_logic_vector(8 downto 0);
   signal nr_palette_priority    : std_logic_vector(1 downto 0);
   signal nr_mmu_we              : std_logic;
   signal nr_mmu                 : std_logic_vector(2 downto 0);
   signal nr_copper_we           : std_logic;
   signal nr_copper_write_8      : std_logic;
   signal nr_68_we               : std_logic;
   signal nr_69_we               : std_logic;
   signal nr_80_we               : std_logic;
   signal nr_8c_we               : std_logic;
   signal nr_8e_we               : std_logic;
   signal nr_8f_we               : std_logic;
   signal nr_c2_we               : std_logic;
   signal nr_c3_we               : std_logic;
   signal nr_c4_we               : std_logic;
   signal nr_c5_we               : std_logic;
   signal nr_c8_we               : std_logic;
   signal nr_c9_we               : std_logic;
   signal nr_ca_we               : std_logic;
   signal nr_ff_we               : std_logic;
   
   signal nr_02_bus_reset        : std_logic;
   signal nr_02_generate_mf_nmi  : std_logic;
   signal nr_02_generate_divmmc_nmi          : std_logic;
   signal nr_03_machine_timing   : std_logic_vector(2 downto 0) := "000";
   signal nr_03_user_dt_lock     : std_logic := '0';
   signal bootrom_en             : std_logic := '1';
   signal eff_bootrom_en         : std_logic := '1';
   signal nr_03_machine_type     : std_logic_vector(2 downto 0) := "000";
   signal nr_04_romram_bank      : std_logic_vector(6 downto 0);
   signal nr_05_joymode_0        : std_logic_vector(2 downto 0);
   signal nr_05_joymode_1        : std_logic_vector(2 downto 0);
   signal nr_05_io_mode          : std_logic;
   signal nr_05_joy0             : std_logic_vector(2 downto 0) := "001";
   signal nr_05_joy1             : std_logic_vector(2 downto 0) := "000";
   signal nr_06_hotkey_cpu_speed_en          : std_logic;
   signal nr_06_hotkey_5060_en   : std_logic;
   signal nr_06_divmmc_automap_en            : std_logic;
   signal nr_06_button_m1_nmi_en : std_logic;
   signal nr_06_ps2_mode         : std_logic := '1';
   signal nr_06_psg_mode         : std_logic_vector(1 downto 0) := "00";
   signal nr_06_internal_speaker_beep        : std_logic := '0';
   signal nr_08_contention_disable           : std_logic := '0';
   signal nr_08_psg_stereo_mode  : std_logic;
   signal nr_08_internal_speaker_en          : std_logic;
   signal nr_08_dac_en           : std_logic;
   signal nr_08_port_ff_rd_en    : std_logic;
   signal nr_08_psg_turbosound_en            : std_logic;
   signal nr_08_keyboard_issue2  : std_logic;
   signal nr_09_psg_mono         : std_logic_vector(2 downto 0);
   signal nr_09_hdmi_audio_disable  : std_logic := '0';
   signal nr_09_sprite_tie       : std_logic;
   signal nr_0a_mf_type          : std_logic_vector(1 downto 0) := "00";
   signal nr_0a_mouse_button_reverse         : std_logic := '0';
   signal nr_0a_mouse_dpi        : std_logic_vector(1 downto 0) := "01";
   signal nr_10_flashboot        : std_logic := '0';
   signal nr_10_coreid           : std_logic_vector(4 downto 0) := "00010";
   signal nr_11_video_timing     : std_logic_vector(2 downto 0) := "000";
   signal nr_12_layer2_active_bank           : std_logic_vector(6 downto 0);
   signal nr_13_layer2_shadow_bank           : std_logic_vector(6 downto 0);
   signal nr_14_global_transparent_rgb       : std_logic_vector(7 downto 0);
   signal nr_15_lores_en         : std_logic;
   signal nr_15_sprite_priority  : std_logic;
   signal nr_15_sprite_border_clip_en        : std_logic;
   signal nr_15_layer_priority   : std_logic_vector(2 downto 0);
   signal nr_15_sprite_over_border_en        : std_logic;
   signal nr_15_sprite_en        : std_logic;
   signal nr_16_layer2_scrollx   : std_logic_vector(7 downto 0);
   signal nr_17_layer2_scrolly   : std_logic_vector(7 downto 0);
   signal nr_18_layer2_clip_x1   : std_logic_vector(7 downto 0);
   signal nr_18_layer2_clip_x2   : std_logic_vector(7 downto 0);
   signal nr_18_layer2_clip_y1   : std_logic_vector(7 downto 0);
   signal nr_18_layer2_clip_y2   : std_logic_vector(7 downto 0);
   signal nr_18_layer2_clip_idx  : std_logic_vector(1 downto 0);
   signal nr_19_sprite_clip_x1   : std_logic_vector(7 downto 0);
   signal nr_19_sprite_clip_x2   : std_logic_vector(7 downto 0);
   signal nr_19_sprite_clip_y1   : std_logic_vector(7 downto 0);
   signal nr_19_sprite_clip_y2   : std_logic_vector(7 downto 0);
   signal nr_19_sprite_clip_idx  : std_logic_vector(1 downto 0);
   signal nr_1a_ula_clip_x1      : std_logic_vector(7 downto 0);
   signal nr_1a_ula_clip_x2      : std_logic_vector(7 downto 0);
   signal nr_1a_ula_clip_y1      : std_logic_vector(7 downto 0);
   signal nr_1a_ula_clip_y2      : std_logic_vector(7 downto 0);
   signal nr_1a_ula_clip_idx     : std_logic_vector(1 downto 0);
   signal nr_1b_tm_clip_x1       : std_logic_vector(7 downto 0);
   signal nr_1b_tm_clip_x2       : std_logic_vector(7 downto 0);
   signal nr_1b_tm_clip_y1       : std_logic_vector(7 downto 0);
   signal nr_1b_tm_clip_y2       : std_logic_vector(7 downto 0);
   signal nr_1b_tm_clip_idx      : std_logic_vector(1 downto 0);
-- signal nr_1c_clip_select      : std_logic_vector(3 downto 0);
-- signal nr_1d_lores_clip_x1    : std_logic_vector(7 downto 0);
-- signal nr_1d_lores_clip_x2    : std_logic_vector(7 downto 0);
-- signal nr_1d_lores_clip_y1    : std_logic_vector(7 downto 0);
-- signal nr_1d_lores_clip_y2    : std_logic_vector(7 downto 0);
-- signal nr_1d_lores_clip_idx   : std_logic_vector(1 downto 0);
   signal nr_22_line_interrupt_en            : std_logic;
   signal nr_23_line_interrupt   : std_logic_vector(8 downto 0);
   signal nr_26_ula_scrollx      : std_logic_vector(7 downto 0);
   signal nr_27_ula_scrolly      : std_logic_vector(7 downto 0);
   signal nr_2d_i2s_sample       : std_logic_vector(1 downto 0);
   signal nr_30_tm_scrollx       : std_logic_vector(9 downto 0);
   signal nr_31_tm_scrolly       : std_logic_vector(7 downto 0);
   signal nr_32_lores_scrollx    : std_logic_vector(7 downto 0);
   signal nr_33_lores_scrolly    : std_logic_vector(7 downto 0);
   signal nr_palette_idx         : std_logic_vector(7 downto 0);
   signal nr_palette_sub_idx     : std_logic;
   signal nr_42_ulanext_format   : std_logic_vector(7 downto 0);
   signal nr_43_palette_autoinc_disable      : std_logic;
   signal nr_43_palette_write_select         : std_logic_vector(2 downto 0);
   signal nr_43_active_sprite_palette        : std_logic;
   signal nr_43_active_layer2_palette        : std_logic;
   signal nr_43_active_ula_palette           : std_logic;
   signal nr_43_ulanext_en       : std_logic;
   signal nr_stored_palette_value            : std_logic_vector(7 downto 0);
   signal nr_4a_fallback_rgb     : std_logic_vector(7 downto 0);
   signal nr_4b_sprite_transparent_index     : std_logic_vector(7 downto 0);
   signal nr_4c_tm_transparent_index         : std_logic_vector(3 downto 0);
   signal nr_copper_addr         : std_logic_vector(10 downto 0);
   signal nr_copper_data_stored  : std_logic_vector(7 downto 0);
   signal nr_62_copper_mode      : std_logic_vector(1 downto 0);
   signal nr_64_copper_offset    : std_logic_vector(7 downto 0);
   signal nr_68_ula_en           : std_logic;
   signal nr_68_blend_mode       : std_logic_vector(1 downto 0);
   signal nr_68_cancel_extended_keys         : std_logic;
   signal nr_68_ula_fine_scroll_x            : std_logic;
   signal nr_68_ula_stencil_mode : std_logic;
   signal nr_6a_lores_radastan   : std_logic;
   signal nr_6a_lores_radastan_xor           : std_logic;
   signal nr_6a_lores_palette_offset         : std_logic_vector(3 downto 0);
   signal nr_6b_tm_en            : std_logic;
   signal nr_6b_tm_control       : std_logic_vector(6 downto 0);
   signal nr_6c_tm_default_attr  : std_logic_vector(7 downto 0);
   signal nr_6e_tilemap_base     : std_logic_vector(5 downto 0);
   signal nr_6e_tilemap_base_7   : std_logic;
   signal nr_6f_tilemap_tiles    : std_logic_vector(5 downto 0);
   signal nr_6f_tilemap_tiles_7  : std_logic;
   signal nr_70_layer2_resolution      : std_logic_vector(1 downto 0);
   signal nr_70_layer2_palette_offset  : std_logic_vector(3 downto 0);
   signal nr_71_layer2_scrollx_msb     : std_logic;
   signal nr_7f_user_register_0  : std_logic_vector(7 downto 0) := X"FF";
   signal nr_98_pi_gpio_o        : std_logic_vector(7 downto 0);
   signal nr_99_pi_gpio_o        : std_logic_vector(7 downto 0);
   signal nr_9a_pi_gpio_o        : std_logic_vector(7 downto 0);
   signal nr_9b_pi_gpio_o        : std_logic_vector(3 downto 0);
   signal nr_81_expbus_ula_override          : std_logic := '0';
   signal nr_81_expbus_nmi_debounce_disable  : std_logic := '0';
   signal nr_81_expbus_clken     : std_logic := '0';
   signal nr_81_expbus_speed     : std_logic_vector(1 downto 0) := "00";
   signal nr_82_internal_port_enable         : std_logic_vector(7 downto 0);
   signal nr_83_internal_port_enable         : std_logic_vector(7 downto 0);
   signal nr_84_internal_port_enable         : std_logic_vector(7 downto 0);
   signal nr_85_internal_port_enable         : std_logic_vector(3 downto 0);
   signal nr_85_internal_port_reset_type     : std_logic := '1';
   signal nr_86_bus_port_enable  : std_logic_vector(7 downto 0);
   signal nr_87_bus_port_enable  : std_logic_vector(7 downto 0);
   signal nr_88_bus_port_enable  : std_logic_vector(7 downto 0);
   signal nr_89_bus_port_enable  : std_logic_vector(3 downto 0);
   signal nr_89_bus_port_reset_type          : std_logic := '1';
   signal nr_8a_bus_port_propagate           : std_logic_vector(5 downto 0);
   signal nr_90_pi_gpio_o_en     : std_logic_vector(7 downto 0) := (others => '0');
   signal nr_91_pi_gpio_o_en     : std_logic_vector(7 downto 0) := (others => '0');
   signal nr_92_pi_gpio_o_en     : std_logic_vector(7 downto 0) := (others => '0');
   signal nr_93_pi_gpio_o_en     : std_logic_vector(3 downto 0) := (others => '0');
   signal nr_a0_pi_peripheral_en : std_logic_vector(7 downto 0);
   signal nr_a2_pi_i2s_ctl       : std_logic_vector(7 downto 0);
-- signal nr_a3_pi_i2s_clkdiv    : std_logic_vector(7 downto 0);
   signal nr_a8_esp_gpio0_en     : std_logic := '0';
   signal nr_a9_esp_gpio0        : std_logic := '1';
   signal nr_c0_im2_vector       : std_logic_vector(2 downto 0);
   signal nr_c0_stackless_nmi    : std_logic;
   signal nr_c0_int_mode_pulse_0_im2_1       : std_logic;
   signal nr_c2_retn_address_lsb : std_logic_vector(7 downto 0);
   signal nr_c3_retn_address_msb : std_logic_vector(7 downto 0);
   signal nr_c4_int_en_0_expbus  : std_logic;
   signal nr_c6_int_en_2_654     : std_logic_vector(2 downto 0);
   signal nr_c6_int_en_2_210     : std_logic_vector(2 downto 0);
   signal nr_cc_dma_int_en_0_10  : std_logic_vector(1 downto 0);
   signal nr_cd_dma_int_en_1     : std_logic_vector(7 downto 0);
   signal nr_ce_dma_int_en_2_654 : std_logic_vector(2 downto 0);
   signal nr_ce_dma_int_en_2_210 : std_logic_vector(2 downto 0);

   signal machine_type_config    : std_logic;
   signal machine_type_48        : std_logic;
   signal machine_type_128       : std_logic;
   signal machine_type_p3        : std_logic;
   
   signal machine_timing_48      : std_logic;
   signal machine_timing_128     : std_logic;
   signal machine_timing_p3      : std_logic;
   signal machine_timing_pentagon            : std_logic;
   
   signal hotkey_cpu_speed       : std_logic;
   signal hotkey_5060            : std_logic;
   signal hotkey_scandouble      : std_logic;
   signal hotkey_scanlines       : std_logic;
   signal hotkey_hard_reset      : std_logic;
   signal hotkey_soft_reset      : std_logic;
   signal hotkey_expbus_enable   : std_logic;
   signal hotkey_expbus_disable  : std_logic;
   signal hotkey_expbus_freeze   : std_logic;
   signal hotkey_m1              : std_logic;
   signal hotkey_drive           : std_logic;
   
   signal nr_07_cpu_speed        : std_logic_vector(1 downto 0);
   signal cpu_speed              : std_logic_vector(1 downto 0) := "00";
   
   signal nr_05_5060             : std_logic := '0';
   signal nr_05_scandouble_en    : std_logic := '1';
   signal nr_09_scanlines        : std_logic_vector(1 downto 0) := "00";
   
   signal nr_02_reset_type       : std_logic_vector(1 downto 0) := "10";
   signal port_253b_dat          : std_logic_vector(7 downto 0);
   signal port_253b_dat_0        : std_logic_vector(7 downto 0);
   
   -- PS/2 KEYMAP & HOT KEYS
   
   signal nr_keymap_addr         : std_logic_vector(8 downto 0) := "000000000";
   signal nr_keymap_dat_msb      : std_logic := '0';
   signal nr_keymap_we           : std_logic;
   signal nr_keymap_dat          : std_logic_vector(7 downto 0);
   
   signal hotkeys_1              : std_logic_vector(10 downto 1) := "0000000000";
   signal hotkeys_0              : std_logic_vector(10 downto 1) := "0000000000";
   signal nr_02_soft_reset       : std_logic;
   signal nr_02_hard_reset       : std_logic;
   
   -- AUDIO
   
   signal audio_ay_reset         : std_logic;
   signal psg_dat                : std_logic_vector(7 downto 0);
   signal pcm_ay_L               : std_logic_vector(11 downto 0);
   signal pcm_ay_R               : std_logic_vector(11 downto 0);
   signal port_fffd_dat          : std_logic_vector(7 downto 0);
   
   signal port_fe_mic_final      : std_logic;
   signal internal_speaker_beep_exclusive    : std_logic;
   
   signal pcm_dac_L              : std_logic_vector(8 downto 0);
   signal pcm_dac_R              : std_logic_vector(8 downto 0);
   
   signal pi_mi2s_sck            : std_logic;
   signal pi_mi2s_ws             : std_logic;
   signal pi_si2s_sck            : std_logic;
   signal pi_si2s_ws             : std_logic;
   signal pi_i2s_sd_o            : std_logic;
   signal pi_i2s_sd_i            : std_logic;
   signal pi_i2s_audio_L         : std_logic_vector(9 downto 0);
   signal pi_i2s_audio_R         : std_logic_vector(9 downto 0);
   
   signal pcm_audio_L            : std_logic_vector(12 downto 0);
   signal pcm_audio_R            : std_logic_vector(12 downto 0);
   
   -- VIDEO
   
   signal cpu_bank5_req          : std_logic;
   signal cpu_bank5_req_dly      : std_logic;
   signal cpu_bank5_sched_dly    : std_logic;
   signal cpu_bank5_sched        : std_logic;
   signal cpu_bank5_do           : std_logic_vector(7 downto 0);
   signal vram_bank5_do0         : std_logic_vector(7 downto 0);
   signal vram_bank5_do1         : std_logic_vector(7 downto 0);
   signal ula_bank_req          : std_logic;
   signal ula_bank_req_dly      : std_logic;
   signal ula_bank_sched_dly    : std_logic;
   signal ula_bank_sched        : std_logic;
   signal ula_bank_do           : std_logic_vector(7 downto 0);
   signal lores_vram_req         : std_logic;
   signal lores_vram_ack_dly     : std_logic;
   signal vram_bank5_a0          : std_logic_vector(13 downto 0);
   signal vram_bank_a1          : std_logic_vector(13 downto 0);
   signal lores_vram_ack         : std_logic;
   
   signal cpu_bank7_do           : std_logic_vector(7 downto 0);
   signal vram_bank7_do          : std_logic_vector(7 downto 0);
   
   signal video_timing_change    : std_logic;
   signal video_timing_change_d  : std_logic := '1';
   
   signal eff_nr_03_machine_timing           : std_logic_vector(2 downto 0) := "000";
   signal eff_nr_05_5060         : std_logic;
   signal eff_nr_05_scandouble_en            : std_logic;
   signal eff_nr_08_contention_disable       : std_logic := '0';
   signal eff_nr_09_scanlines    : std_logic_vector(1 downto 0);
   
   signal ula_int_en             : std_logic_vector(1 downto 0);
   signal hc                     : unsigned(8 downto 0);
   signal vc                     : unsigned(8 downto 0);
   signal phc                    : unsigned(8 downto 0);
   signal whc                    : unsigned(8 downto 0);
   signal wvc                    : unsigned(8 downto 0);
   signal cvc                    : unsigned(8 downto 0);
   signal rgb_hsync_n            : std_logic;
   signal rgb_vsync_n            : std_logic;
   signal rgb_hblank_n           : std_logic;
   signal rgb_vblank_n           : std_logic;
   
   signal pulse_int_n            : std_logic;
   signal ula_int_pulse          : std_logic;
   signal line_int_pulse         : std_logic;
   signal pulse_count_end        : std_logic;
   signal pulse_count            : std_logic_vector(4 downto 0);

   signal layer_priorities_0     : std_logic_vector(2 downto 0);
   signal ula_en_0               : std_logic;
   signal ula_stencil_mode_0     : std_logic;
   signal ula_blend_mode_0       : std_logic_vector(1 downto 0);
   signal ulanext_en_0           : std_logic;
   signal ulanext_format_0       : std_logic_vector(7 downto 0);
   signal ulap_en_0              : std_logic;
   signal lores_en_0             : std_logic;
   signal sprite_en_0            : std_logic;
   signal tm_en_0                : std_logic;
   signal transparent_rgb_0      : std_logic_vector(7 downto 0);
   signal fallback_rgb_0         : std_logic_vector(7 downto 0);
   signal ula_palette_select_0   : std_logic;
   signal tm_palette_select_0    : std_logic;
   signal layer2_palette_select_0            : std_logic;
   signal sprite_palette_select_0            : std_logic;

   signal lores_pixel_1          : std_logic_vector(7 downto 0);
   signal lores_pixel_en_1a      : std_logic;
   signal layer2_pixel_1         : std_logic_vector(7 downto 0);
   signal sprite_pixel_1         : std_logic_vector(7 downto 0);
   signal sprite_pixel_en_1a     : std_logic;
   signal ula_pixel_1            : std_logic_vector(7 downto 0);
   signal ula_select_bgnd_1      : std_logic;
   signal tm_pixel_1             : std_logic_vector(7 downto 0);
   signal tm_pixel_en_1          : std_logic;
   signal tm_pixel_below_1       : std_logic;
   signal tm_pixel_textmode_1    : std_logic;
   signal ula_border_1           : std_logic;
   signal ula_clipped_1          : std_logic;
   signal layer_priorities_1     : std_logic_vector(2 downto 0);
   signal video_blank_n_1        : std_logic;
   signal rgb_vsync_n_1          : std_logic;
   signal rgb_vblank_n_1         : std_logic;
   signal rgb_hblank_n_1         : std_logic;
   signal rgb_hsync_n_1          : std_logic;
   signal ula_en_1               : std_logic;
   signal ula_en_1a              : std_logic;
   signal ula_stencil_mode_1     : std_logic;
   signal ula_stencil_mode_1a    : std_logic;
   signal ula_blend_mode_1       : std_logic_vector(1 downto 0);
   signal ula_blend_mode_1a      : std_logic_vector(1 downto 0);
   signal lores_en_1             : std_logic;
   signal lores_en_1a            : std_logic;
   signal sprite_en_1            : std_logic;
   signal sprite_en_1a           : std_logic;
   signal tm_en_1                : std_logic;
   signal tm_en_1a               : std_logic;
   signal transparent_rgb_1      : std_logic_vector(7 downto 0);
   signal transparent_rgb_1a     : std_logic_vector(7 downto 0);
   signal fallback_rgb_1         : std_logic_vector(7 downto 0);
   signal fallback_rgb_1a        : std_logic_vector(7 downto 0);
   signal ula_palette_select_1   : std_logic;
   signal ula_palette_select_1a  : std_logic;
   signal tm_palette_select_1    : std_logic;
   signal tm_palette_select_1a   : std_logic;
   signal layer2_palette_select_1            : std_logic;
   signal layer2_palette_select_1a           : std_logic;
   signal sprite_palette_select_1            : std_logic;
   signal sprite_palette_select_1a           : std_logic;
   signal lores_pixel_en_1       : std_logic;
   signal layer2_pixel_en_1      : std_logic;
   signal sprite_pixel_en_1      : std_logic;
   
   signal nr_palette_index       : std_logic_vector(9 downto 0);
   signal nr_palette_index_utm   : std_logic_vector(9 downto 0);
   signal nr_palette_dat         : std_logic_vector(10 downto 0);
   signal nr_palette_rd          : std_logic;
   signal nr_ulatm_we            : std_logic;
   signal nr_ulatm_palette_dat   : std_logic_vector(15 downto 0);
   signal ulatm_rgb_1            : std_logic_vector(15 downto 0);
   signal ulalores_pixel_1       : std_logic_vector(7 downto 0);
   signal ulatm_pixel_1          : std_logic_vector(9 downto 0);
   signal ula_rgb_1              : std_logic_vector(8 downto 0);
   signal ula_rgb_2              : std_logic_vector(8 downto 0);
   signal tm_rgb_2               : std_logic_vector(8 downto 0);
-- signal lores_rgb_2            : std_logic_vector(8 downto 0);
   signal nr_l2s_palette_we      : std_logic;
   signal nr_l2s_palette_dat     : std_logic_vector(15 downto 0);
   signal l2s_prgb_1             : std_logic_vector(15 downto 0);
   signal l2s_pixel_1            : std_logic_vector(9 downto 0);
   signal layer2_prgb_1          : std_logic_vector(9 downto 0);
   signal layer2_rgb_2           : std_logic_vector(8 downto 0);
   signal layer2_priority_2      : std_logic;
   signal sprite_rgb_2           : std_logic_vector(8 downto 0);
   signal ula_en_2               : std_logic;
   signal ula_border_2           : std_logic;
   signal ula_clipped_2          : std_logic;
   signal ula_stencil_mode_2     : std_logic;
   signal ula_blend_mode_2       : std_logic_vector(1 downto 0);
-- signal lores_en_2             : std_logic;
   signal tm_en_2                : std_logic;
   signal tm_pixel_en_2          : std_logic;
   signal tm_pixel_below_2       : std_logic;
   signal tm_pixel_textmode_2    : std_logic;
   signal layer2_pixel_en_2      : std_logic;
   signal sprite_pixel_en_2      : std_logic;
   signal transparent_rgb_2      : std_logic_vector(7 downto 0);
   signal fallback_rgb_2         : std_logic_vector(7 downto 0);
   signal layer_priorities_2     : std_logic_vector(2 downto 0);
   signal video_blank_n_2        : std_logic;
   signal rgb_vsync_n_2          : std_logic;
   signal rgb_vblank_n_2         : std_logic;
   signal rgb_hblank_n_2         : std_logic;
   signal rgb_hsync_n_2          : std_logic;
   
   signal ula_mix_transparent    : std_logic;
   signal ula_mix_rgb            : std_logic_vector(8 downto 0);
   signal mix_top_transparent    : std_logic;
   signal mix_top_rgb            : std_logic_vector(8 downto 0);
   signal mix_bot_transparent    : std_logic;
   signal mix_bot_rgb            : std_logic_vector(8 downto 0);
   signal ula_transparent        : std_logic;
   signal ula_rgb                : std_logic_vector(8 downto 0);
-- signal lores_transparent      : std_logic;
-- signal lores_rgb              : std_logic_vector(8 downto 0);
   signal tm_transparent         : std_logic;
   signal tm_rgb                 : std_logic_vector(8 downto 0);
   signal stencil_transparent    : std_logic;
   signal stencil_rgb            : std_logic_vector(8 downto 0);
   signal ulatm_transparent      : std_logic;
   signal ulatm_rgb              : std_logic_vector(8 downto 0);
   signal sprite_transparent     : std_logic;
   signal sprite_rgb             : std_logic_vector(8 downto 0);
   signal layer2_transparent     : std_logic;
   signal layer2_rgb             : std_logic_vector(8 downto 0);
   signal layer2_priority        : std_logic;
   signal ula_final_rgb          : std_logic_vector(8 downto 0);
   signal ula_final_transparent  : std_logic;
   signal mix_rgb                : std_logic_vector(8 downto 0);
   signal mix_rgb_transparent    : std_logic;
   signal rgb_out_2              : std_logic_vector(8 downto 0);
   signal rgb_out_2a             : std_logic_vector(8 downto 0);

   signal rgb_vsync_n_7          : std_logic;
   signal rgb_vsync_n_6          : std_logic;
   signal rgb_vsync_n_5          : std_logic;
   signal rgb_vsync_n_4          : std_logic;
   signal rgb_vsync_n_3          : std_logic;
   signal rgb_vblank_n_7         : std_logic;
   signal rgb_vblank_n_6         : std_logic;
   signal rgb_vblank_n_5         : std_logic;
   signal rgb_vblank_n_4         : std_logic;
   signal rgb_vblank_n_3         : std_logic;
   signal rgb_hblank_n_7         : std_logic;
   signal rgb_hblank_n_6         : std_logic;
   signal rgb_hblank_n_5         : std_logic;
   signal rgb_hblank_n_4         : std_logic;
   signal rgb_hblank_n_3         : std_logic;
   signal rgb_hsync_n_7          : std_logic;
   signal rgb_hsync_n_6          : std_logic;
   signal rgb_hsync_n_5          : std_logic;
   signal rgb_hsync_n_4          : std_logic;
   signal rgb_hsync_n_3          : std_logic;
   signal rgb_out_7              : std_logic_vector(8 downto 0);
   signal rgb_out_6              : std_logic_vector(8 downto 0);
   signal rgb_out_5              : std_logic_vector(8 downto 0);
   signal rgb_out_4              : std_logic_vector(8 downto 0);
   signal rgb_out_3              : std_logic_vector(8 downto 0);
   
   signal rgb_vsync_n_o          : std_logic;
   signal rgb_vblank_n_o         : std_logic;
   signal rgb_hblank_n_o         : std_logic;
   signal rgb_hsync_n_o          : std_logic;
   signal rgb_out_o              : std_logic_vector(8 downto 0);
   signal rgb_csync_n_o          : std_logic;

begin

   ------------------------------------------------------------
   -- OUTPUT --------------------------------------------------
   ------------------------------------------------------------

   o_CPU_SPEED <= cpu_speed;  
   o_CPU_CONTEND <= ula_cpu_contend;
   o_CPU_CLK_LSB <= hc(0);

   o_RESET_SOFT <= nr_02_soft_reset;
   o_RESET_HARD <= nr_02_hard_reset;
   o_RESET_PERIPHERAL <= nr_02_bus_reset;

   o_FLASH_BOOT <= nr_10_flashboot;
   o_CORE_ID <= nr_10_coreid;

   o_KBD_CANCEL <= nr_68_cancel_extended_keys;
   o_KBD_ROW <= keyrow;

   o_KEYMAP_ADDR <= nr_keymap_addr;
   o_KEYMAP_DATA <= nr_keymap_dat;
   o_KEYMAP_WE <= nr_keymap_we;

   o_JOY_IO_MODE_EN <= nr_05_joy_iomode_en;
   o_JOY_IO_MODE_PIN_7 <= joy_iomode_pin7;

   o_PS2_MODE <= nr_06_ps2_mode;
   o_MOUSE_CONTROL <= nr_0a_mouse_button_reverse & nr_0a_mouse_dpi;
   
   o_I2C_SCL_n <= i2c_scl_o;
   o_I2C_SDA_n <= i2c_sda_o;
   
   o_SPI_SS_FLASH_n <= spi_ss_flash_n;
   o_SPI_SS_SD1_n <= spi_ss_sd1_n;
   o_SPI_SS_SD0_n <= spi_ss_sd0_n;

   o_SPI_SCK <= spi_sck;
   o_SPI_MOSI <= spi_mosi;

   o_UART0_TX <= uart0_tx_esp;

   o_RGB <= rgb_out_o;
   o_RGB_CS_n <= rgb_csync_n_o;
   o_RGB_VS_n <= rgb_vsync_n_o;
   o_RGB_HS_n <= rgb_hsync_n_o;
   o_RGB_VB_n <= rgb_vblank_n_o;
   o_RGB_HB_n <= rgb_hblank_n_o;
      
   o_VIDEO_50_60 <= eff_nr_05_5060;
   o_VIDEO_SCANLINES <= eff_nr_09_scanlines;
   o_VIDEO_SCANDOUBLE <= eff_nr_05_scandouble_en;
   
   o_VIDEO_MODE <= nr_11_video_timing;
   o_MACHINE_TIMING <= eff_nr_03_machine_timing;
   
   o_HDMI_RESET <= video_timing_change_d;
   
   o_AUDIO_HDMI_AUDIO_EN <= not nr_09_hdmi_audio_disable;
   
   o_AUDIO_SPEAKER_EN <= nr_08_internal_speaker_en;
   o_AUDIO_SPEAKER_BEEP <= internal_speaker_beep_exclusive;
   
   o_AUDIO_MIC <= port_fe_mic xor pi_fe_ear;
   
   o_AUDIO_SPEAKER_EAR <= port_fe_ear;
   o_AUDIO_SPEAKER_MIC <= port_fe_mic_final;
   
   o_AUDIO_L <= pcm_audio_L;
   o_AUDIO_R <= pcm_audio_R;

   o_RAM_A_ADDR <= sram_addr;
   o_RAM_A_REQ <= sram_req_t;
   o_RAM_A_RD <= sram_rd;
   o_RAM_A_DO <= cpu_do;

   o_RAM_B_ADDR <= layer2_addr_eff;
   o_RAM_B_REQ_T <= layer2_req_t;

   o_BUS_ADDR <= cpu_a;
   o_BUS_DO <= cpu_do;
   o_BUS_MREQ_n <= bus_mreq_n;
   o_BUS_IORQ_n <= bus_iorq_n;
   o_BUS_RD_n <= cpu_rd_n;
   o_BUS_WR_n <= cpu_wr_n;
   o_BUS_M1_n <= cpu_m1_n;
   o_BUS_INT_n <= pulse_int_n;
   o_BUS_BUSAK_n <= '1';
   o_BUS_HALT_n <= cpu_halt_n;
   o_BUS_RFSH_n <= cpu_rfsh_n;
-- o_BUS_IEO <= im2_ieo;

   o_BUS_EN <= expbus_eff_en;
   o_BUS_CLKEN <= expbus_eff_clken;
   
   o_BUS_NMI_DEBOUNCE_DISABLE <= nr_81_expbus_nmi_debounce_disable;

   o_ESP_GPIO_0 <= nr_a9_esp_gpio0;
   o_ESP_GPIO_0_EN <= nr_a8_esp_gpio0_en;

   o_GPIO <= pi_gpio_o(27 downto 22) & gpio_21 & gpio_20 & gpio_19 & gpio_18 & gpio_17 & gpio_16 & gpio_15 & gpio_14 & pi_gpio_o(13 downto 12) & gpio_11 & gpio_10 & pi_gpio_o(9) & gpio_08 & gpio_07 & pi_gpio_o(6 downto 4) & gpio_03 & gpio_02 & pi_gpio_o(1 downto 0);
   o_GPIO_EN <= pi_gpio_en(27 downto 22) & gpio_21_en & gpio_20_en & gpio_19_en & gpio_18_en & gpio_17_en & gpio_16_en & gpio_15_en & gpio_14_en & pi_gpio_en(13 downto 12) & gpio_11_en & gpio_10_en & gpio_09_en & gpio_08_en & gpio_07_en & pi_gpio_en(6 downto 4) & gpio_03_en & gpio_02_en & pi_gpio_en(1 downto 0);

   ------------------------------------------------------------
   -- RESET ---------------------------------------------------
   ------------------------------------------------------------
   
   -- incoming reset signals are asserted for some time by the top level module
   
   reset <= reset_hard or reset_soft;
   
   reset_soft <= i_RESET_SOFT;
   reset_hard <= i_RESET_HARD;
   
   ------------------------------------------------------------
   -- Z80 & DMA -----------------------------------------------
   ------------------------------------------------------------

   cpu_mod: entity work.T80na
   generic map (
      Mode        => 0
   )
   port map (
      RESET_n     => not reset,     -- in
      CLK_n       => i_CLK_CPU,     -- in
      WAIT_n      => z80_wait_n,    -- in
      INT_n       => z80_int_n,     -- in
      NMI_n       => z80_nmi_n,     -- in (detection is on rising edge of cpu clock)
      BUSRQ_n     => z80_busrq_n,   -- in
      M1_n        => z80_m1_n,      -- out
      MREQ_n      => z80_mreq_n,    -- out
      IORQ_n      => z80_iorq_n,    -- out
      RD_n        => z80_rd_n,      -- out
      WR_n        => z80_wr_n,      -- out
      RFSH_n      => z80_rfsh_n,    -- out
      HALT_n      => z80_halt_n,    -- out
      BUSAK_n     => z80_busak_n,   -- out
      A           => z80_a,         -- out
      D_i         => cpu_di,        -- in
      D_o         => z80_do,        -- out
      -- extended functions
      Z80N_dout_o       => Z80N_dout_s,
      Z80N_data_o       => Z80N_data_s,
      Z80N_command_o    => Z80N_command_s
   );
   
   dma_mod: entity work.z80dma
   port map (
      reset_i        => reset,
      clk_i          => i_CLK_CPU,
      turbo_i        => cpu_speed,
      dma_mode_i     => dma_mode,       -- 0 = zxn dma, 1 = z80 dma

      dma_en_wr_s    => port_dma_wr,    -- allow dma to program itself? ans: no
      dma_en_rd_s    => port_dma_rd,

      cpu_d_i        => z80_do,
      wait_n_i       => dma_wait_n,
      dma_delay_i    => im2_dma_delay,

      bus_busreq_n_i => '1',            -- busreq in daisy chain (i_BUS_BUSREQ_n)
      cpu_busreq_n_o => dma_busrq_n,    -- busreq out
         
      cpu_bai_n      => z80_busak_n,    -- busak in daisy chain
      cpu_bao_n      => open,           -- busak out daisy chain

      dma_a_o        => dma_a,
      dma_d_o        => dma_do,
      dma_d_i        => cpu_di,
      dma_rd_n_o     => dma_rd_n,
      dma_wr_n_o     => dma_wr_n,
      dma_mreq_n_o   => dma_mreq_n,
      dma_iorq_n_o   => dma_iorq_n,

      cpu_d_o        => port_dma_dat_0
   );
   
   process (i_CLK_CPU)
   begin
      if falling_edge(i_CLK_CPU) then
         port_dma_dat <= port_dma_dat_0;
      end if;
   end process;
   
   process (i_CLK_CPU)
   begin
      if falling_edge(i_CLK_CPU) then
         if reset = '1' then
            dma_mode <= '0';
         elsif port_dma_rd = '1' or port_dma_wr = '1' then
            dma_mode <= port_0b_lsb;
         end if;
      end if;
   end process;
   
   -- no dma controller on the expansion bus at this time

-- dma_holds_bus <= '1' when dma_busrq_n = '0' and z80_busak_n = '0' else '0';
   dma_holds_bus <= '1' when z80_busak_n = '0' else '0';
   
   cpu_m1_n <= '1' when dma_holds_bus = '1' else z80_m1_n;
   cpu_mreq_n <= dma_mreq_n when dma_holds_bus = '1' else (z80_mreq_n or z80_stackless_nmi);
   cpu_iorq_n <= dma_iorq_n when dma_holds_bus = '1' else z80_iorq_n;
   cpu_rd_n <= dma_rd_n when dma_holds_bus = '1' else z80_rd_n;
   cpu_wr_n <= dma_wr_n when dma_holds_bus = '1' else z80_wr_n;
   cpu_rfsh_n <= '1' when dma_holds_bus = '1' else z80_rfsh_n;
   cpu_halt_n <= '1' when dma_holds_bus = '1' else z80_halt_n;
   cpu_a <= dma_a when dma_holds_bus = '1' else z80_a;
   cpu_do <= dma_do when dma_holds_bus = '1' else z80_do;

   z80_wait_n <= '0' when (ula_wait_n = '0') or (ulap_wait_n = '0') or (sram_wait_n = '0') or (i_BUS_WAIT_n = '0' and expbus_eff_en = '1') or (i_CPU_WAIT = '1') else '1';
   z80_int_n <= pulse_int_n and im2_int_n and (i_BUS_INT_n or (not expbus_eff_en) or expbus_eff_disable_io or (not im2_ieo) or (not nr_c4_int_en_0_expbus));
   z80_nmi_n <= nmi_generate_n;
   z80_busrq_n <= dma_busrq_n;
   
   dma_wait_n <= z80_wait_n and spi_wait_n;

   process (z80_stackless_nmi, dma_holds_bus, z80_retn_address, cpu_mreq_n, cpu_rfsh_n, cpu_a, eff_bootrom_en, bootrom_do, 
      sram_romcs, eff_expbus_romcs_replace, i_BUS_DI, sram_bank5, cpu_bank5_do, sram_bank7, cpu_bank7_do, i_RAM_A_DI, 
      cpu_iorq_n, port_internal_rd_response, bus_iorq_ula, port_rd_dat, im2_vector_en, im2_vector, expbus_eff_en, expbus_eff_disable_io)
   begin
      if z80_stackless_nmi = '1' and dma_holds_bus = '0' then
      
         cpu_di <= z80_retn_address;
         
      elsif cpu_mreq_n = '0' and cpu_rfsh_n = '1' then
      
         if cpu_a(15 downto 14) = "00" and eff_bootrom_en = '1' then
            cpu_di <= bootrom_do;
         elsif sram_romcs = '1' and eff_expbus_romcs_replace = '0' then
            cpu_di <= i_BUS_DI;
         elsif sram_bank5 = '1' then
            cpu_di <= cpu_bank5_do;
         elsif sram_bank7 = '1' then
            cpu_di <= cpu_bank7_do;
         else
            cpu_di <= i_RAM_A_DI;
         end if;

      elsif cpu_iorq_n = '0' then
      
         if port_internal_rd_response = '1' and bus_iorq_ula = '0' then
            cpu_di <= port_rd_dat;
         elsif im2_vector_en = '1' then
            cpu_di <= im2_vector;
         elsif expbus_eff_en = '1' and expbus_eff_disable_io = '0' then
            cpu_di <= i_BUS_DI;
         else
            cpu_di <= X"FF";
         end if;
         
      else
         cpu_di <= X"FF";
      end if;
   end process;

   --
   -- maskable interrupts
   --

   -- reti decoder
   
   im2ctl_mod: entity work.im2_control
   port map (
      i_CLK_CPU         => i_CLK_CPU,
      i_reset           => reset,
      
      i_m1_n            => cpu_m1_n,
      i_mreq_n          => cpu_mreq_n,
      i_iorq_n          => cpu_iorq_n,
      
      i_rd_n            => cpu_rd_n,
      i_wr_n            => cpu_wr_n,
      
      i_cpu_d           => cpu_di,

      o_reti_decode     => im2_reti_decode,
      o_reti_seen       => z80_reti_seen_t3,
      
      o_retn_seen       => z80_retn_seen_t3,
      
      o_dma_delay       => dma_delay
   );

   process (i_CLK_28)
   begin
      if rising_edge(i_CLK_28) then
         if reset = '1' then
            z80_retn_seen_28_d <= '0';
         else
            z80_retn_seen_28_d <= z80_retn_seen_t3;
         end if;
      end if;
   end process;
   
   z80_retn_seen_28 <= z80_retn_seen_t3 and not z80_retn_seen_28_d;

   -- peripheral interrupt handlers
   
   -- priority order is bit 0 (highest) to bit 13 (lowest)
   -- priority number also corresponds to interrupt vector
   --
   --      0 = line
   --      1 = uart0 rx
   --      2 = uart1 rx
   --   3:10 = ctc 0-7
   --     11 = ula
   --     12 = uart0 tx
   --     13 = uart1 tx   
   
   im2_int_req <= uart1_tx_empty & uart0_tx_empty & ula_int_pulse & ctc_zc_to & 
      (uart1_rx_near_full or (uart1_rx_avail and not nr_c6_int_en_2_654(1))) & 
      (uart0_rx_near_full or (uart0_rx_avail and not nr_c6_int_en_2_210(1))) & 
      line_int_pulse;
   
   im2_int_en <= nr_c6_int_en_2_654(2) & nr_c6_int_en_2_210(2) & ula_int_en(0) & ctc_int_en & 
      (nr_c6_int_en_2_654(1) or nr_c6_int_en_2_654(0)) & (nr_c6_int_en_2_210(1) or nr_c6_int_en_2_210(0)) & ula_int_en(1);

   im2_status_clear <= (nr_ca_we and nr_wr_dat(6)) & (nr_ca_we and nr_wr_dat(2)) & (nr_c8_we and nr_wr_dat(0)) & 
      ((nr_c9_we & nr_c9_we & nr_c9_we & nr_c9_we & nr_c9_we & nr_c9_we & nr_c9_we & nr_c9_we) and nr_wr_dat) & 
      (nr_ca_we and (nr_wr_dat(5) or nr_wr_dat(4))) & (nr_ca_we and (nr_wr_dat(1) or nr_wr_dat(0))) & 
      (nr_c8_we and nr_wr_dat(1));
   
   im2_dma_int_en <= nr_ce_dma_int_en_2_654(2) & nr_ce_dma_int_en_2_210(2) & nr_cc_dma_int_en_0_10(0) & nr_cd_dma_int_en_1 &
      (nr_ce_dma_int_en_2_654(1) or nr_ce_dma_int_en_2_654(0)) & (nr_ce_dma_int_en_2_210(1) or nr_ce_dma_int_en_2_210(0)) & nr_cc_dma_int_en_0_10(1);
   
   im2per_mod: entity work.peripherals
   generic map (
      NUM_PERIPH           => 14,
      VEC_BITS             => 4
   )
   port map (
      i_CLK_28             => i_CLK_28,
      i_CLK_CPU            => i_CLK_CPU,
      i_reset              => reset,
      
      i_m1_n               => cpu_m1_n,
      i_iorq_n             => cpu_iorq_n,
      
      i_mode_pulse_0_im2_1 => nr_c0_int_mode_pulse_0_im2_1,
   
      i_int_req            => im2_int_req,
      i_int_en             => im2_int_en,
      
      o_int_status         => im2_int_status,    -- CLK_28
      i_int_status_clear   => im2_status_clear,  -- CLK_28
      
      i_iei                => '1',
      o_ieo                => im2_ieo,
      
      i_reti_decode        => im2_reti_decode,
      i_reti_seen          => z80_reti_seen_t3,
   
      o_int_n              => im2_int_n,
      o_vector             => im2_vec,
      
      i_dma_int_en         => im2_dma_int_en,
      o_dma_int            => im2_dma_int,
      
      o_pulse_en           => pulse_int_en
   );

   im2_vector_en <= '1' when cpu_m1_n = '0' and cpu_iorq_n = '0' and im2_ieo = '0' else '0';  -- and nr_c0_int_mode_pulse_0_im2_1 = '1' else '0';
   im2_vector <= nr_c0_im2_vector & im2_vec & '0';

   process (i_CLK_CPU)
   begin
      if rising_edge(i_CLK_CPU) then
         if reset = '1' then
            im2_dma_delay <= '0';
         elsif dma_delay = '0' then
            im2_dma_delay <= im2_dma_int and nr_c0_int_mode_pulse_0_im2_1;
         end if;
      end if;
   end process;

   -- pulsed interrupt
   -- duration is fixed at ~32 cpu cycles and must be asserted immediately

   process (i_CLK_28)
   begin
      -- int is sampled on rising edge of cpu clock
      if falling_edge(i_CLK_28) then
         if reset = '1' then
            pulse_int_n <= '1';
         elsif pulse_int_n = '1' then
            if pulse_int_en = '1' then
               pulse_int_n <= '0';
            end if;
         elsif pulse_count_end = '1' then
            pulse_int_n <= '1';
         end if;
      end if;
   end process;
   
   pulse_count_end <= '1' when pulse_count = "11111" else '0';
   
   process (i_CLK_CPU)
   begin
      if rising_edge(i_CLK_CPU) then
         if pulse_int_n = '1' then
            pulse_count <= (others => '0');
         elsif pulse_count_end = '0' then
            pulse_count <= pulse_count + 1;
         end if;
      end if;
   end process;
   
   --
   -- nmi
   --

   -- stackless nmi response
   
   z80_stackless_nmi <= '1' when nr_c0_stackless_nmi = '1' and (Z80N_command_s = NMIACK_LSB or Z80N_command_s = NMIACK_MSB or Z80N_command_s = RETN_LSB or Z80N_command_s = RETN_MSB) else '0';
   
   process (i_CLK_28)
   begin
      if rising_edge(i_CLK_28) then
         if reset = '1' then
            nr_c2_retn_address_lsb <= (others => '0');
            nr_c3_retn_address_msb <= (others => '0');
         elsif (Z80N_command_s = NMIACK_LSB) and cpu_wr_n = '0' then
            nr_c2_retn_address_lsb <= cpu_do;
         elsif (Z80N_command_s = NMIACK_MSB) and cpu_wr_n = '0' then
            nr_c3_retn_address_msb <= cpu_do;
         elsif nr_c2_we = '1' then
            nr_c2_retn_address_lsb <= nr_wr_dat;
         elsif nr_c3_we = '1' then
            nr_c3_retn_address_msb <= nr_wr_dat;
         end if;
      end if;
   end process;

   z80_retn_address <= nr_c2_retn_address_lsb when Z80N_command_s = RETN_LSB else nr_c3_retn_address_msb;

   -- first come first serve
   
   process (i_CLK_28)
   begin
      if rising_edge(i_CLK_28) then
         if reset = '1' then
            nmi_expbus_en <= '1';
         elsif nmi_expbus = '1' then
            nmi_expbus_en <= '0';
         elsif i_BUS_NMI_n = '1' then
            nmi_expbus_en <= '1';
         end if;
      end if;
   end process;

   nmi_assert_expbus <= '1' when expbus_eff_en = '1' and expbus_eff_disable_mem = '0' and i_BUS_NMI_n = '0' else '0';
   
   nmi_activated <= nmi_mf or nmi_divmmc or nmi_expbus;
   
   process (i_CLK_28)
   begin
      if rising_edge(i_CLK_28) then
         if reset = '1' or nmi_state = S_NMI_END or machine_type_config = '1' then
            nmi_mf <= '0';
            nmi_divmmc <= '0';
            nmi_expbus <= '0';
         elsif nmi_activated = '0' then
            if hotkey_m1 = '1' and nr_06_button_m1_nmi_en = '1' and port_e3_reg(7) = '0' and divmmc_nmi_hold = '0' then
               nmi_mf <= '1';
            elsif hotkey_drive = '1' and nr_06_divmmc_automap_en = '1' and mf_is_active = '0' then
               nmi_divmmc <= '1';
            elsif nmi_expbus_en = '1' and nmi_assert_expbus = '1' then
               nmi_expbus <= '1';
            end if;
         end if;
      end if;
   end process;
   
   nmi_hold <= mf_nmi_hold when nmi_mf = '1' else divmmc_nmi_hold when nmi_divmmc = '1' else nmi_assert_expbus;
   
   -- nmi state machine
   
   nmi_holding <= '1' when nmi_hold = '1' or dma_holds_bus = '1' else '0';
   nmi_opus <= '1' when nmi_mf = '1' and nr_81_expbus_nmi_debounce_disable = '1' and nmi_assert_expbus = '1' else '0';
   
   process (nmi_state, nmi_activated, nmi_holding, nmi_opus)
   begin
      case nmi_state is
         when S_NMI_IDLE =>
            if nmi_activated = '1' then
               nmi_state_next <= S_NMI_ASSERT;
            else
               nmi_state_next <= S_NMI_IDLE;
            end if;
         when S_NMI_ASSERT =>
            nmi_state_next <= S_NMI_HOLD;
         when S_NMI_OPUS =>                    -- separate to avoid button activation in multiface
            if nmi_opus = '1' then
               nmi_state_next <= S_NMI_OPUS;
            else
               nmi_state_next <= S_NMI_HOLD;
            end if;
         when S_NMI_HOLD  =>
            if nmi_holding = '0' then
               nmi_state_next <= S_NMI_END;
            elsif nmi_opus = '1' then          -- multiface + opus discovery
               nmi_state_next <= S_NMI_OPUS;
            else
               nmi_state_next <= S_NMI_HOLD;
            end if;
--       when S_NMI_END =>
--          nmi_state_next <= S_NMI_IDLE;
         when others =>
            nmi_state_next <= S_NMI_IDLE;
      end case;
   end process;
   
   process (i_CLK_CPU)
   begin
      if rising_edge(i_CLK_CPU) then
         if reset = '1' or machine_type_config = '1' then
            nmi_state <= S_NMI_IDLE;
         else
            nmi_state <= nmi_state_next;
         end if;
      end if;
   end process;
   
   nmi_generate_n <= '0' when nmi_state = S_NMI_ASSERT or nmi_state = S_NMI_OPUS else '1';
   nmi_mf_button <= '1' when nmi_mf = '1' and nmi_state = S_NMI_ASSERT else '0';
   nmi_divmmc_button <= '1' when nmi_divmmc = '1' and nmi_state = S_NMI_ASSERT else '0';

   ------------------------------------------------------------
   -- EXPANSION BUS -------------------------------------------
   ------------------------------------------------------------
   
   --
   -- expansion bus control (changed during iowr to port 253b or nextreg instruction)
   --
   
   hotkey_expbus_freeze <= '1' when (port_divmmc_io_en_diff = '1' and divmmc_automap_held = '1') or (port_multiface_io_en_diff = '1' and mf_mem_en = '1') else '0';
   
   process (i_CLK_28)
   begin
      if rising_edge(i_CLK_28) then
         if reset_hard = '1' then
            nr_80_expbus <= (others => '0');
         elsif reset_soft = '1' then
            nr_80_expbus(7 downto 4) <= nr_80_expbus(3 downto 0);
         elsif nr_80_we = '1' then
            nr_80_expbus <= nr_wr_dat;
         elsif hotkey_expbus_enable = '1' and hotkey_expbus_freeze = '0' then
            nr_80_expbus(7) <= '1';
         elsif hotkey_expbus_disable = '1' and hotkey_expbus_freeze = '0' then
            nr_80_expbus(7) <= '0';
         end if;
      end if;
   end process;

   expbus_en <= nr_80_expbus(7);
   expbus_romcs_replace <= nr_80_expbus(6);
   expbus_disable_io <= nr_80_expbus(5);
   expbus_disable_mem <= nr_80_expbus(4);
   
   expbus_clken <= nr_81_expbus_clken;
   expbus_speed <= nr_81_expbus_speed;
   
   --
   -- expansion bus connection
   --
   
   -- filter io cycles
   -- external devices should see port fe, memory paging

   port_propagate_fe <= port_fe and nr_8a_bus_port_propagate(0);
   port_propagate_7ffd <= port_7ffd and nr_8a_bus_port_propagate(1);
   port_propagate_dffd <= port_dffd and nr_8a_bus_port_propagate(2);
   port_propagate_1ffd <= port_1ffd and nr_8a_bus_port_propagate(3);
   port_propagate_ff <= port_ff and nr_8a_bus_port_propagate(4);
   port_propagate_eff7 <= port_eff7 and nr_8a_bus_port_propagate(5);

   port_propagate <= port_propagate_fe or port_propagate_7ffd or port_propagate_dffd or port_propagate_1ffd or port_propagate_ff or port_propagate_eff7;
   
   bus_iorq_n <= cpu_iorq_n or (cpu_m1_n and ((port_internal_response or expbus_eff_disable_io) and not port_propagate));
   bus_mreq_n <= cpu_mreq_n or ((expbus_eff_disable_mem or (not cpu_a(15) and (not cpu_a(14)) and not sram_romcs_en)) and cpu_rfsh_n);

-- o_BUS_ADDR <= cpu_a;
-- o_BUS_DO <= cpu_do;
-- o_BUS_MREQ_n <= bus_mreq_n;
-- o_BUS_IORQ_n <= bus_iorq_n;
-- o_BUS_RD_n <= cpu_rd_n;
-- o_BUS_WR_n <= cpu_wr_n;
-- o_BUS_M1_n <= cpu_m1_n;
-- o_BUS_INT_n <= pulse_int_n;
-- o_BUS_BUSAK_n <= '1';
-- o_BUS_HALT_n <= cpu_halt_n;
-- o_BUS_RFSH_n <= cpu_rfsh_n;

   ------------------------------------------------------------
   -- ALTERNATE ROM -------------------------------------------
   ------------------------------------------------------------

   process (i_CLK_28)
   begin
      if rising_edge(i_CLK_28) then
         if reset_hard = '1' then
            nr_8c_altrom <= (others => '0');
         elsif reset_soft = '1' then
            nr_8c_altrom(7 downto 4) <= nr_8c_altrom(3 downto 0);
         elsif nr_8c_we = '1' then
            nr_8c_altrom <= nr_wr_dat;
         end if;
      end if;
   end process;
   
   nr_8c_altrom_en <= nr_8c_altrom(7);
   nr_8c_altrom_rw <= nr_8c_altrom(6);
   nr_8c_altrom_lock_rom1 <= nr_8c_altrom(5);
   nr_8c_altrom_lock_rom0 <= nr_8c_altrom(4);

   ------------------------------------------------------------
   -- PI GPIO -------------------------------------------------
   ------------------------------------------------------------

   -- https://elinux.org/RPi_BCM2835_GPIOs
   
   -- todo: video in, video out, memory mapping, z80 bus
   
   pi_gpio_en <= nr_93_pi_gpio_o_en & nr_92_pi_gpio_o_en & nr_91_pi_gpio_o_en & nr_90_pi_gpio_o_en;
   pi_gpio_o <= nr_9b_pi_gpio_o & nr_9a_pi_gpio_o & nr_99_pi_gpio_o & nr_98_pi_gpio_o;
   
   pi_uart_rxtx <= nr_a0_pi_peripheral_en(5);
   pi_uart_en <= nr_a0_pi_peripheral_en(4);
   pi_i2c1_en <= nr_a0_pi_peripheral_en(3);
   pi_spi0_en <= nr_a0_pi_peripheral_en(0);
   
   pi_i2s_en <= nr_a2_pi_i2s_ctl(7) or nr_a2_pi_i2s_ctl(6);
   pi_i2s_enL <= nr_a2_pi_i2s_ctl(7);
   pi_i2s_enR <= nr_a2_pi_i2s_ctl(6);
   pi_i2s_inout <= nr_a2_pi_i2s_ctl(4);
   pi_i2s_muteL <= nr_a2_pi_i2s_ctl(3);
   pi_i2s_muteR <= nr_a2_pi_i2s_ctl(2);
-- pi_i2s_slave <= nr_a2_pi_i2s_ctl(1);
   pi_i2s_ear <= nr_a2_pi_i2s_ctl(0);

   -- spi0 7,8,9,10,11
   
   gpio_08_en <= '1' when pi_spi0_en = '1' else pi_gpio_en(8);
   gpio_08 <= spi_ss_rpi0_n when pi_spi0_en = '1' else pi_gpio_o(8);
   
   gpio_07_en <= '1' when pi_spi0_en = '1' else pi_gpio_en(7);
   gpio_07 <= spi_ss_rpi1_n when pi_spi0_en = '1' else pi_gpio_o(7);
   
   gpio_09_en <= '0' when pi_spi0_en = '1' else pi_gpio_en(9);
   pi_spi0_miso <= i_GPIO(9) when pi_spi0_en = '1' else '1';
   
   gpio_10_en <= '1' when pi_spi0_en = '1' else pi_gpio_en(10);
   gpio_10 <= spi_mosi when pi_spi0_en = '1' else pi_gpio_o(10);
   
   gpio_11_en <= '1' when pi_spi0_en = '1' else pi_gpio_en(11);
   gpio_11 <= spi_sck when pi_spi0_en = '1' else pi_gpio_o(11);

   -- i2c1 2,3
   
   gpio_02_en <= not i2c_sda_o when pi_i2c1_en = '1' else pi_gpio_en(2);
   gpio_02 <= '0' when pi_i2c1_en = '1' else pi_gpio_o(2);
   
   gpio_03_en <= not i2c_scl_o when pi_i2c1_en = '1' else pi_gpio_en(3);
   gpio_03 <= '0' when pi_i2c1_en = '1' else pi_gpio_o(3);
   
   pi_i2c1_sda <= i_GPIO(2) when pi_i2c1_en = '1' else '1';
   pi_i2c1_scl <= i_GPIO(3) when pi_i2c1_en = '1' else '1';

   -- uart 14,15(,16,17) (need to cross wires for pi!)
   -- connect Rx to GPIO14 if pi_uart_rxtx = 1

   gpio_14_en <= not pi_uart_rxtx when pi_uart_en = '1' else pi_gpio_en(14);
   gpio_15_en <= pi_uart_rxtx when pi_uart_en = '1' else pi_gpio_en(15);
   gpio_16_en <= pi_uart_rxtx when pi_uart_en = '1' and uart1_hwflow_en = '1' else pi_gpio_en(16);
   gpio_17_en <= not pi_uart_rxtx when pi_uart_en = '1' and uart1_hwflow_en = '1' else pi_gpio_en(17);
   
   gpio_14 <= uart1_tx_pi when pi_uart_en = '1' else pi_gpio_o(14);
   gpio_15 <= uart1_tx_pi when pi_uart_en = '1' else pi_gpio_o(15);
   gpio_16 <= pi_uart_rtr_n when pi_uart_en = '1' and uart1_hwflow_en = '1' else pi_gpio_o(16);
   gpio_17 <= pi_uart_rtr_n when pi_uart_en = '1' and uart1_hwflow_en = '1' else pi_gpio_o(17);
   
   pi_uart_rx <= (i_GPIO(14) and pi_uart_rxtx) or (i_GPIO(15) and not pi_uart_rxtx) when pi_uart_en = '1' else '1';
   pi_uart_cts_n <= (i_GPIO(17) and pi_uart_rxtx) or (i_GPIO(16) and not pi_uart_rxtx) when pi_uart_en = '1' and uart1_hwflow_en = '1' else '0';

   -- i2s 18,19,20,21
   
-- gpio_18_en <= '1' when pi_i2s_en = '1' and pi_i2s_slave = '0' else '0' when pi_i2s_en = '1' and pi_i2s_slave = '1' else pi_gpio_en(18);
-- gpio_19_en <= '1' when pi_i2s_en = '1' and pi_i2s_slave = '0' else '0' when pi_i2s_en = '1' and pi_i2s_slave = '1' else pi_gpio_en(19);
   gpio_18_en <= '0' when pi_i2s_en = '1' else pi_gpio_en(18);
   gpio_19_en <= '0' when pi_i2s_en = '1' else pi_gpio_en(19);
   gpio_20_en <= pi_i2s_inout when pi_i2s_en = '1' else pi_gpio_en(20);
   gpio_21_en <= not pi_i2s_inout when pi_i2s_en = '1' else pi_gpio_en(21);
   
   gpio_18 <= pi_mi2s_sck when pi_i2s_en = '1' else pi_gpio_o(18);
   gpio_19 <= pi_mi2s_ws when pi_i2s_en = '1' else pi_gpio_o(19);
   gpio_20 <= pi_i2s_sd_o when pi_i2s_en = '1' else pi_gpio_o(20);
   gpio_21 <= pi_i2s_sd_o when pi_i2s_en = '1' else pi_gpio_o(21);
   
   pi_i2s_sd_i <= ((i_GPIO(21) and pi_i2s_inout) or (i_GPIO(20) and not pi_i2s_inout)) and pi_i2s_en;
   
-- pi_si2s_sck <= i_GPIO(18) and pi_i2s_en and pi_i2s_slave;
-- pi_si2s_ws <= i_GPIO(19) and pi_i2s_en and pi_i2s_slave;

   pi_si2s_sck <= i_GPIO(18) and pi_i2s_en;
   pi_si2s_ws <= i_GPIO(19) and pi_i2s_en;
   
   pi_audio_L <= ("10" & X"00") when (pi_i2s_en = '0' or pi_i2s_muteL = '1' or pi_i2s_ear = '1') else pi_i2s_audio_L when pi_i2s_enL = '1' else pi_i2s_audio_R;
   pi_audio_R <= ("10" & X"00") when (pi_i2s_en = '0' or pi_i2s_muteR = '1' or pi_i2s_ear = '1') else pi_i2s_audio_R when pi_i2s_enR = '1' else pi_i2s_audio_L;

   pi_fe_threshold <= pi_i2s_audio_L(9 downto 8) or pi_i2s_audio_R(9 downto 8);
   
   process (i_CLK_28)
   begin
      if rising_edge(i_CLK_28) then
         if pi_i2s_en = '0' or pi_i2s_ear = '0' then
            pi_fe_ear <= '0';
         elsif pi_fe_ear = '1' and pi_fe_threshold = "00" then
            pi_fe_ear <= '0';
         elsif pi_fe_ear = '0' and pi_fe_threshold = "11" then
            pi_fe_ear <= '1';
         end if;
      end if;
   end process;

   --
   -- pi gpio output
   --

-- o_GPIO <= ...
-- o_GPIO_EN <= ...


   ------------------------------------------------------------
   -- PORT DECODING -------------------------------------------
   ------------------------------------------------------------

   -- todo: investigate switching to pentagon method where decoding depends on instruction type "IN A,(n)" vs "IN r,(C)"

   --
   -- active port enables (changed during iowr to port 253b or nextreg instruction)
   --
   
   internal_port_enable <= (nr_85_internal_port_enable & nr_84_internal_port_enable & nr_83_internal_port_enable & nr_82_internal_port_enable) when expbus_eff_en = '0' else
                           ((nr_89_bus_port_enable and nr_85_internal_port_enable) & (nr_88_bus_port_enable and nr_84_internal_port_enable) & (nr_87_bus_port_enable and nr_83_internal_port_enable) & (nr_86_bus_port_enable and nr_82_internal_port_enable));
   
   --
   
   port_ff_io_en <= internal_port_enable(0);
   
   port_7ffd_io_en <= internal_port_enable(1);
   port_dffd_io_en <= internal_port_enable(2);
   port_1ffd_io_en <= internal_port_enable(3);
   
   port_p3_floating_bus_io_en <= internal_port_enable(4);
   
   port_dma_6b_io_en <= internal_port_enable(5);
   
   port_1f_io_en <= internal_port_enable(6);
   port_37_io_en <= internal_port_enable(7);
   
   --

   port_divmmc_io_en <= internal_port_enable(8);
   port_divmmc_io_en_diff <= nr_83_internal_port_enable(0) xor nr_87_bus_port_enable(0);
   
   port_multiface_io_en <= internal_port_enable(9);
   port_multiface_io_en_diff <= nr_83_internal_port_enable(1) xor nr_87_bus_port_enable(1);
   
   port_i2c_io_en <= internal_port_enable(10);
   port_spi_io_en <= internal_port_enable(11);
   port_uart_io_en <= internal_port_enable(12);
   
   port_mouse_io_en <= internal_port_enable(13);
   port_sprite_io_en <= internal_port_enable(14);
   port_layer2_io_en <= internal_port_enable(15);
   
   --
   
   port_ay_io_en <= internal_port_enable(16);
   port_dac_sd1_ABCD_1f0f4f5f_io_en <= internal_port_enable(17);   -- soundrive mode 1
   port_dac_sd2_ABCD_f1f3f9fb_io_en <= internal_port_enable(18);   -- soundrive mode 2
   port_dac_stereo_AD_3f5f_io_en <= internal_port_enable(19);   -- profi covox
   port_dac_stereo_BC_0f4f_io_en <= internal_port_enable(20);   -- covox
   port_dac_mono_AD_fb_io_en <= internal_port_enable(21) and not port_dac_sd2_ABCD_f1f3f9fb_io_en;   -- pentagon / atm (when mode 2 is off)
   port_dac_mono_BC_b3_io_en <= internal_port_enable(22);   -- gs covox
   port_dac_mono_AD_df_io_en <= internal_port_enable(23);   -- specdrum
   
   --
   
   port_ulap_io_en <= internal_port_enable(24);
   port_dma_0b_io_en <= internal_port_enable(25);
   port_eff7_io_en <= internal_port_enable(26);
   port_ctc_io_en <= internal_port_enable(27);
   
   --
   -- peripheral disable
   -- do not alter port decoding during an io cycle (nextreg changes can occur at any time)
   --

   process (i_CLK_28)
   begin
      if rising_edge(i_CLK_28) then
         if cpu_mreq_n = '0' then
         
            port_1f_hw_en <= joyL_1f_en or joyR_1f_en;
            port_37_hw_en <= joyL_37_en or joyR_37_en;
            
            p3_timing_hw_en <= machine_timing_p3;
            s128_timing_hw_en <= machine_timing_128;
            
            dac_hw_en <= nr_08_dac_en;

         end if;
      end if;
   end process;
   
   process (i_CLK_28)
   begin
      if rising_edge(i_CLK_28) then
         if cpu_iorq_n = '1' or memcycle_delay_complete = '0' then
            bus_iorq_ula <= expbus_eff_en and i_BUS_IORQULA_n and port_fe and cpu_m1_n and not expbus_eff_disable_io;
         else
            bus_iorq_ula <= '0';
         end if;
      end if;
   end process;

   --
   -- early decode of port addresses to allow filtering of io cycles to expansion bus
   --
   
   process (cpu_a(15 downto 8))
   begin
   
      port_00xx_msb <= '0';
      port_04xx_msb <= '0';
      port_05xx_msb <= '0';
      port_10xx_msb <= '0';
      port_11xx_msb <= '0';
      port_12xx_msb <= '0';
      port_1fxx_msb <= '0';
      port_24xx_msb <= '0';
      port_25xx_msb <= '0';
      port_30xx_msb <= '0';
      port_3dxx_msb <= '0';
      port_7fxx_msb <= '0';
      port_bfxx_msb <= '0';
      port_fexx_msb <= '0';
      port_ffxx_msb <= '0';
      
      case cpu_a(15 downto 8) is
      
         when X"00"  => port_00xx_msb <= '1';
         when X"04"  => port_04xx_msb <= '1';
         when X"05"  => port_05xx_msb <= '1';
         when X"10"  => port_10xx_msb <= '1';
         when X"11"  => port_11xx_msb <= '1';
         when X"12"  => port_12xx_msb <= '1';
         when X"1F"  => port_1fxx_msb <= '1';
         when X"24"  => port_24xx_msb <= '1';
         when X"25"  => port_25xx_msb <= '1';
         when X"30"  => port_30xx_msb <= '1';
         when X"3D"  => port_3dxx_msb <= '1';
         when X"7F"  => port_7fxx_msb <= '1';
         when X"BF"  => port_bfxx_msb <= '1';
         when X"FE"  => port_fexx_msb <= '1';
         when X"FF"  => port_ffxx_msb <= '1';
         when others => null;
      
      end case;
   
   end process;
   
   process (cpu_a(7 downto 0))
   begin
   
      port_00_lsb <= '0';
      port_08_lsb <= '0';
      port_0b_lsb <= '0';
      port_0f_lsb <= '0';
      port_1f_lsb <= '0';
      port_37_lsb <= '0';
      port_38_lsb <= '0';
      port_3f_lsb <= '0';
      port_3b_lsb <= '0';
      port_4f_lsb <= '0';
      port_57_lsb <= '0';
      port_5b_lsb <= '0';
      port_5f_lsb <= '0';
      port_62_lsb <= '0';
      port_66_lsb <= '0';
      port_6b_lsb <= '0';
      port_b3_lsb <= '0';
      port_c6_lsb <= '0';
      port_df_lsb <= '0';
      port_e3_lsb <= '0';
      port_e7_lsb <= '0';
      port_eb_lsb <= '0';
      port_f1_lsb <= '0';
      port_f3_lsb <= '0';
      port_f7_lsb <= '0';
      port_f9_lsb <= '0';
      port_fb_lsb <= '0';
      port_ff_lsb <= '0';
   
      case cpu_a(7 downto 0) is
   
         when X"00"  => port_00_lsb <= '1';
         when X"08"  => port_08_lsb <= '1';
         when X"0B"  => port_0b_lsb <= '1';
         when X"0F"  => port_0f_lsb <= '1';
         when X"1F"  => port_1f_lsb <= '1';
         when X"37"  => port_37_lsb <= '1';
         when X"38"  => port_38_lsb <= '1';
         when X"3F"  => port_3f_lsb <= '1';
         when X"4F"  => port_4f_lsb <= '1';
         when X"57"  => port_57_lsb <= '1';
         when X"5B"  => port_5b_lsb <= '1';
         when X"5F"  => port_5f_lsb <= '1';
         when X"3B"  => port_3b_lsb <= '1';
         when X"62"  => port_62_lsb <= '1';
         when X"66"  => port_66_lsb <= '1';
         when X"6B"  => port_6b_lsb <= '1';
         when X"B3"  => port_b3_lsb <= '1';
         when X"C6"  => port_c6_lsb <= '1';
         when X"DF"  => port_df_lsb <= '1';
         when X"E3"  => port_e3_lsb <= '1';
         when X"E7"  => port_e7_lsb <= '1';
         when X"EB"  => port_eb_lsb <= '1';
         when X"F1"  => port_f1_lsb <= '1';
         when X"F3"  => port_f3_lsb <= '1';
         when X"F7"  => port_f7_lsb <= '1';
         when X"F9"  => port_f9_lsb <= '1';
         when X"FB"  => port_fb_lsb <= '1';
         when X"FF"  => port_ff_lsb <= '1';
         when others => null;

      end case;

   end process;
   
   port_fd <= '1' when cpu_a(1 downto 0) = "01" else '0';

   -- ula/scld
   
   port_fe <= '1' when cpu_a(0) = '0' else '0';
   port_ff <= '1' when port_ff_lsb = '1' else '0';
   
   port_fe_override <= '1' when cpu_a(7 downto 4) = "0000" and nr_81_expbus_ula_override = '1' else '0';
   
   -- +3 floating bus
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
